AudioMorphology/Europi/kicad/europi_main_v2/europi main v2 board front.png

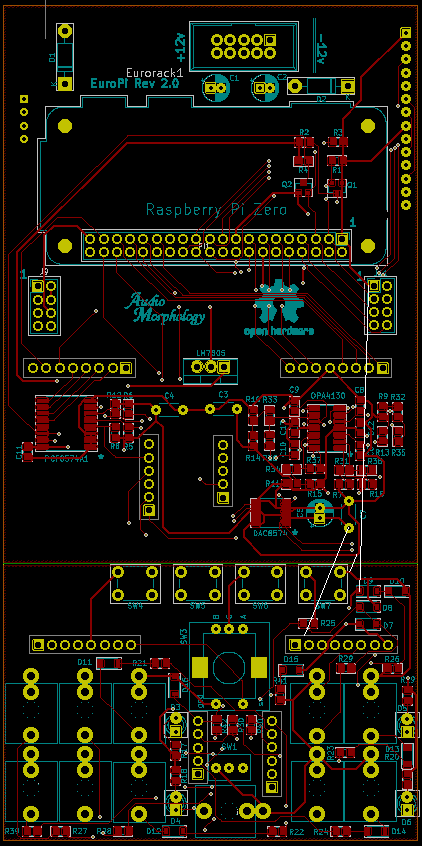
kicad/europi_main_v2/europi main v2 board front.png
