AudioMorphology/Europi/kicad/europi_main_v2/europi main v2 board rear.png

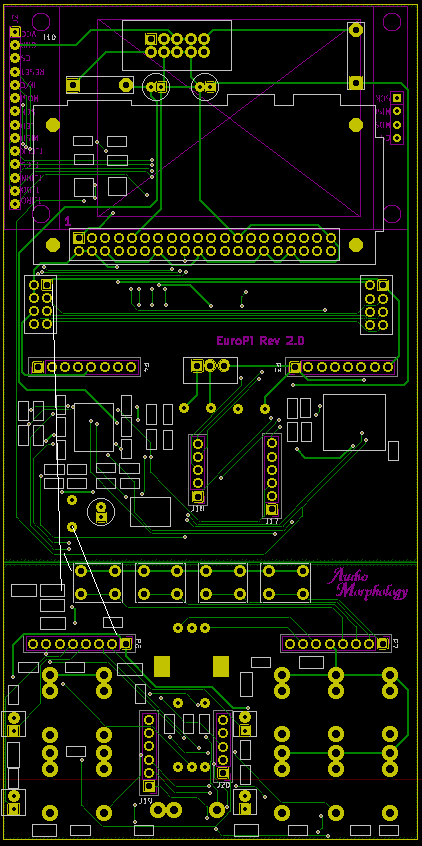
kicad/europi_main_v2/europi main v2 board rear.png
