AudioMorphology/Europi/quantizer_scales.h

// Copyright 2016 Richard R. Goodwin / Audio Morphology / Olivier Gillet
//
// Authors: Richard R. Goodwin (richard.goodwin@morphology.co.uk)
//          Olivier Gillet (ol.gillet@gmail.com)
//
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
// See http://creativecommons.org/licenses/MIT/ for more information.
//-------------------------------------------------------------------------------

// The values in the scale_values array and, indeed, the names of the various scales
// came from the Mutable Instruments Braids software, released by Olivier Gillet 
// under a CC License. So, I have incorporated the same license, and have included 
// Olivier's License declaration, below, to make it clear that I am not claiming 
// ownership or proprietary rights over any aspects of these quantisation scales

//-------------------------------------------------------------------------------
// Copyright 2015 Olivier Gillet.
//
// Author: Olivier Gillet (ol.gillet@gmail.com)
//
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
// See http://creativecommons.org/licenses/MIT/ for more information.
//
// -----------------------------------------------------------------------------

/*
 * QUANTIZATION SCALES
 * 
 * These arrays set the Lower and Upper boundaries for
 * a given note in a given scale, and identify the absolute
 * value that should be returned.
 * 
 * Values are based on 6000 discrete values per Octave
 */

static int lower_boundary[49][12] = {
{0},
{0,250,750,1250,1750,2250,2750,3250,3750,4250,4750,5250},
{0,500,1500,2250,3000,4000,5000},
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
{0,1020,1930,2488,3512,3961,5441},
//43: m_kauns
{0,1020,2039,2488,3961,4980},
//44: Bairagi
{0,449,2488,3512,4980},
//45: b_todi
{0,449,1469,3512,4980},
//46: Chandradeep
{0,1469,2488,3512,4980},
//47: Kaushik_todi
{0,1469,2488,2949,3961},
//48: Jogeshwari
{0,1469,1930,2488,4422,4980}
};


// Number of Notes in each particular scale
static int scale_notes[49] = {
  // Off
  0,
  // Semitones
  12,
  // Ionian (From midipal/BitT source code)
  7,
  // Dorian (From midipal/BitT source code)
  7,
  // Phrygian (From midipal/BitT source code)
  7,
  // Lydian (From midipal/BitT source code)
  7,
  // Mixolydian (From midipal/BitT source code)
  7,
  // Aeolian (From midipal/BitT source code)
  7,
  // Locrian (From midipal/BitT source code)
  7,
  // Blues major (From midipal/BitT source code)
  6,
  // Blues minor (From midipal/BitT source code)
  6,
  // Pentatonic major (From midipal/BitT source code)
  5,
  // Pentatonic minor (From midipal/BitT source code)
  5,
  // Folk (From midipal/BitT source code)
  8,
  // Japanese (From midipal/BitT source code)
  5,
  // Gamelan (From midipal/BitT source code)
  5,
  // Gypsy
  7,
  // Arabian
  7,
  // Flamenco
  7,
  // Whole tone (From midipal/BitT source code)
  6,
  // pythagorean (From yarns source code)
  12,
  // 1_4_eb (From yarns source code)
  12,
  // 1_4_e (From yarns source code)
  12,
  // 1_4_ea (From yarns source code)
  12,
  // bhairav (From yarns source code)
  7,
  // gunakri (From yarns source code)
  5,
  // marwa (From yarns source code)
  6,
  // shree (From yarns source code)
  7,
  // purvi (From yarns source code)
  7,
  // bilawal (From yarns source code)
  7,
  // yaman (From yarns source code)
  7,
  // kafi (From yarns source code)
  7,
  // bhimpalasree (From yarns source code)
  7,
  // darbari (From yarns source code)
  7,
  // rageshree (From yarns source code)
  7,
  // khamaj (From yarns source code)
  8,
  // mimal (From yarns source code)
  8,
  // parameshwari (From yarns source code)
  6,
  // rangeshwari (From yarns source code)
  6,
  // gangeshwari (From yarns source code)
  6,
  // kameshwari (From yarns source code)
  6,
  // pa__kafi (From yarns source code)
  7,
  // natbhairav (From yarns source code)
  7,
  // m_kauns (From yarns source code)
  6,
  // bairagi (From yarns source code)
  5,
  // b_todi (From yarns source code)
  5,
  // chandradeep (From yarns source code)
  5,
  // kaushik_todi (From yarns source code)
  5,
  // jogeshwari (From yarns source code)
  6
};

// Array of strings representing the name of each scale
static const char * scale_names[] = {
"Off",
"Semitones",
"Ionian",
"Dorian",
"Phrygian", 
"Lydian",
"Mixolydian",
"Aeolian", 
"Locrian", 
"Blues Major", 
"Blues Minor", 
"Pentatonic Major", 
"Pentatonic Minor", 
"Folk", 
"Japanese", 
"Gamelan", 
"Gypsy", 
"Arabian", 
"Flamenco", 
"Whole Tone", 
"Pythagorean", 
"1_4_eb", 
"1_4_e", 
"1_4_ea", 
"bhairav", 
"Gunakri", 
"Marwa", 
"Shree", 
"Purvi", 
"Bilawal", 
"Kafi", 
"Bhimpalascree", 
"Darbari", 
"Rageshree", 
"Khamaj", 
"Mimal", 
"Parameshwari", 
"Rangeshwari", 
"Gangeshwari", 
"Kameshwari", 
"pa__kafi", 
"Natbhairav", 
"m_kauns", 
"Bairagi", 
"b_todi", 
"Chandradeep", 
"Kaushik_todi", 
"Jogeshwari"
};
