AudioMorphology/Europi/bjorklund.h

// Copyright 2016 Richard R. Goodwin / Audio Morphology / Tim Churches
//
// Authors: Richard R. Goodwin (richard.goodwin@morphology.co.uk)
//          Tim Churches: https://github.com/timchurches
//
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
// See http://creativecommons.org/licenses/MIT/ for more information.
//-------------------------------------------------------------------------------

// The values in the tables below were computed by Tim Churches using a Python
// implementation of E. Bjorklund's algorithm from his paper entitled 'The Theory 
// of Rep-Rate Pattern Generation in the SNS Timing Systems' and released under 
// the licence below, which I include in full.

//--------------------------------------------------------------------------------
// Copyright (c) 2016 Tim Churches
//
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
// Bjorklund (Euclidean) patterns, generated by resources/bjorklund.py

/* All that these are are bit-wise patterns representing the 'most symmetrical' 
 * distribution of a given number of triggers within a given number of beats.
 * 
 * Bjorklund's aglorithm uses a recursive method for dividing beats into steps
 * and then dividing any remaining beats into those etc etc.
 * 
 * The end result is surprisingly musical, and generates rhythms that are 
 * recognisable from various cultures.
 */
static uint32_t bjorklund_patterns[31][33] = {
// 2 step patterns
{0,1,3,0,0,0,0,0,0,0,0,0,0,0,0,0,0,0,0,0,0,0,0,0,0,0,0,0,0,0,0,0,0 }, 
// 3 step patterns
{0,1,3,7,0,0,0,0,0,0,0,0,0,0,0,0,0,0,0,0,0,0,0,0,0,0,0,0,0,0,0,0,0 }, 
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
{0,1,16385,1049601,2113665,17043521,34636833,17895697,71600273,71901769,153391689,153692457,88757413,156543573,89478485,357913941,223783765,359356085,229485997,230087533,249263835,250469819,393705335,259776247,264174575,401596351,268173055,402644991,268435455,536870911,0,0,0},
// 30 step patterns
{0,1,32769,1049601,4227201,17043521,34636833,69345553,143167761,76620873,153391689,306858313,173184165,312822421,178951509,357913941,715838805,448096981,727373493,460025197,460175067,767258331,501070779,518977399,519552495,528349151,803200959,536346111,536854527,536870911,1073741823,0,0},
// 31 step patterns
{0,1,32769,1049601,16843009,17043521,34636833,138682897,286331153,287458441,153391689,345133641,614802729,623530661,357739093,357913941,1431655765,1432005461,900422325,917878189,1457216365,1533916891,997649883,1002159035,1038020471,1593294319,1602090975,1069531071,1610087935,1610596351,1073741823,2147483647,0},
// 32 step patterns
{0,1,65537,4196353,16843009,67641409,69272609,142885409,286331153,304367761,306778697,1227133513,1229539657,1246925989,1251297941,1252693333,1431655765,1789580629,1792371413,1801115317,1835887981,1840700269,3067852507,3077496251,2004318071,3151884023,3186605551,2130442207,2139062143,2146434559,2147450879,2147483647,4294967295 }
};
