AudioMorphology/Europi/europi_gui.c

// Copyright 2016 Richard R. Goodwin / Audio Morphology
//
// Author: Richard R. Goodwin (richard.goodwin@morphology.co.uk)
//
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
// See http://creativecommons.org/licenses/MIT/ for more information.

#include <stdio.h>
#include <string.h>
#include "europi.h"
#include "../raylib/src/raylib.h"

extern int clock_freq;
extern int step_ticks;
extern int prog_running;
extern int run_stop; 
extern int save_run_stop;
extern int last_track;
extern int SingleChannelOffset;
extern Vector2 touchPosition;
extern int currentGesture;
extern int lastGesture;
extern menu Menu[]; 
extern char input_txt[]; 
extern char current_filename[];
extern char modal_dialog_txt1[];
extern char modal_dialog_txt2[];
extern char modal_dialog_txt3[];
extern char modal_dialog_txt4[];
extern Texture2D KeyboardTexture;
extern Texture2D DialogTexture;
extern Texture2D SmallDialogTexture;
extern Texture2D TextInputTexture;
extern Texture2D Text2chTexture;
extern Texture2D Text5chTexture;
extern Texture2D Text10chTexture;
extern Texture2D MainScreenTexture;
extern Texture2D TopBarTexture;
extern Texture2D ButtonBarTexture; 
extern Texture2D VerticalScrollBarTexture;
extern Texture2D VerticalScrollBarShortTexture;
extern Texture2D ScrollHandleTexture;
extern int VerticalScrollPercent;
extern char *kbd_chars[4][11];
extern char debug_messages[10][80];
extern int next_debug_slot;
extern int kbd_char_selected;
extern int selected_step;
extern enum encoder_focus_t encoder_focus;
extern enum btnA_func_t btnA_func;
extern enum btnB_func_t btnB_func;
extern enum btnC_func_t btnC_func;
extern enum btnD_func_t btnD_func;
extern int btnA_state;
extern int btnB_state;
extern int btnC_state;
extern int btnD_state;
extern int edit_track;
extern int edit_step;
//extern struct screen_overlays ScreenOverlays;
extern uint32_t ActiveOverlays;
extern enum display_page_t DisplayPage;
extern struct europi Europi;
extern char **files;
extern size_t file_count;                      
extern int file_selected;
extern int first_file;
extern int debug;
extern pthread_attr_t detached_attr;		
extern pthread_t ThreadId; 


/*
 * GUI_8x8 Attempts to display more detail in a subset of tracks and steps
 * 8 Tracks x 8 Steps
 */
void gui_8x8(void){
    Rectangle stepRectangle = {0,0,0,0};
    Rectangle trackRectangle = {0,0,0,0};
    int start_track,track, column;
    int step, offset, txt_len;
    char txt[20]; 
    /* Depending on the total number of tracks, and the position 
     * of the vertical scroll bar, the starting track will vary
     */
    if(last_track > 8){
        start_track = ((last_track-8) * VerticalScrollPercent) / 100;
        /* Don't display the Vertical Scroll Bar in certain situations */
        if(ActiveOverlays & ovl_Keyboard) { 
			ActiveOverlays &= ~ovl_VerticalScrollBar;
        }
        else {
            ActiveOverlays |= ovl_VerticalScrollBar;
        }
    }
    else {
        start_track = 0;
        ActiveOverlays &= ~ovl_VerticalScrollBar;
    }
    BeginDrawing();
    DrawTexture(MainScreenTexture,0,0,WHITE);
	int vOffset = 0;
	if(ShortScroll()) vOffset=20;
    for(track = 0; track < 8; track++){
        // Can only display 8 tracks, so need to know which
        // track we are starting with, and display the next 7
        offset = Europi.tracks[start_track+track].current_step / 8;
        sprintf(txt,"%02d-%d:",start_track+track+1,(offset * 8)+1);
        txt_len = MeasureText(txt,20);
        if(start_track+track < last_track){
            DrawText(txt,68-txt_len,12+(vOffset+(track * 25)),20,DARKGRAY);
            DrawRectangleLines(4,vOffset+8+(track * 25),67,26,DARKGRAY);
        } else {
            // in-active tracks greyed-out
            DrawText(txt,68-txt_len,12+(vOffset+(track * 25)),20,LIGHTGRAY);
            DrawRectangleLines(4,vOffset+8+(track * 25),67,26,LIGHTGRAY);
        }
        // Check for Track select
        trackRectangle.x = 4;
        trackRectangle.y = vOffset + 8 + (track * 25);
        trackRectangle.width = 67;
        trackRectangle.height = 26;
		// Only if no menus or overlays active, and this track isn't beyond the end track
		if (CheckCollisionPointRec(touchPosition, trackRectangle) && (currentGesture != GESTURE_NONE) && (start_track+track < last_track)){
			if(OverlayActive( ovl_VerticalScrollBar ) == 0){
                // Open this track in a Single Channel view
                edit_track = start_track+track;
                select_track(start_track+track);
                ClearScreenOverlays();
                SwitchChannelFunction(edit_track);
				encoder_focus = track_select;
            }
			else {
				// Just update the selected track
				select_track(start_track+track);
				encoder_focus = track_select;
			}
        }
        for(column=0;column<8;column++){
            stepRectangle.x = 70 + (column * 25);
            stepRectangle.y = vOffset + 10 + (track * 25);
            stepRectangle.width = 22;
            stepRectangle.height = 22;
            if(start_track+track < last_track) {
                // Check gesture collision
                if (CheckCollisionPointRec(touchPosition, stepRectangle) && (currentGesture == GESTURE_DOUBLETAP)){
                    if(OverlayActive(ovl_VerticalScrollBar) == 0){
                    // Only if no Menus or Overlays active
                        // Open this step in the Single Step editor
                        edit_track = start_track+track;
                        edit_step = (offset*8)+column;
                        select_track(start_track+track);
                        ClearScreenOverlays();
                        DisplayPage = SingleStep;
                        ActiveOverlays |= ovl_SingleStep; 
                        encoder_focus = step_select;
                        btnA_func = btnA_none;
                        btnB_func = btnB_prev;
                        btnC_func = btnC_next;
                        btnD_func = btnD_done; 
                        save_run_stop = run_stop;
                    }
                    else {
                        select_track(start_track+track);
                        edit_step = (offset*8)+column;
                        encoder_focus = step_select;
                    }
                }
                if((offset*8)+column >= Europi.tracks[start_track+track].last_step){
                    // beyond the last step, just paint black squares
                    DrawRectangleRec(stepRectangle, BLACK); 
                }
                else if((offset*8)+column == Europi.tracks[start_track+track].current_step){
                    // Paint current step
                    DrawRectangleRec(stepRectangle, LIME);   
                }
                else {
                    // paint blank step
                    DrawRectangleRec(stepRectangle, MAROON); 
                }
            }
            else {
                DrawRectangleRec(stepRectangle,LIGHTGRAY);
            }
        }  
        // Print the end-step number at the RHS of each row
        sprintf(txt,":%d",(offset * 8)+8);
        if(start_track+track < last_track) {
            DrawText(txt,270,12+(vOffset+(track * 25)),20,DARKGRAY);
        }
        else {
            DrawText(txt,270,12+(vOffset+(track * 25)),20,LIGHTGRAY);
        }
    }
    // Handle any screen overlays - these need to 
    // be added within the Drawing loop
    ShowScreenOverlays();
    EndDrawing();
}
/*
 * GUI_SINGLESTEP enables editing of all params 
 * to do with a single step
 */
void gui_singlestep(void){
    int column, offset, txt_len;
    char txt[20]; 
    Rectangle stepRectangle = {0,0,0,0};
    Rectangle touchRectangle = {0,0,0,0};
    BeginDrawing();
    DrawTexture(MainScreenTexture,0,0,WHITE);
    // Items to cover:
    // Track Type (CV / MIDI)
    // Quantization
    // Pitch
    // Gate / Trigger
    // Slew
    // Step Repeat
    // DrawRectangle(6,29, 308, 183, CLR_LIGHTBLUE);  
    // Draw the current Track 8-Step segement
    offset = edit_step / 8; //Europi.tracks[edit_track].current_step / 8;
    sprintf(txt,"%02d-%d:",edit_track+1,(offset * 8)+1);
    txt_len = MeasureText(txt,20);
    DrawText(txt,68-txt_len,34,20,DARKGRAY);
	// Check for tap on this to switch to Track view
	touchRectangle.x = 8;
	touchRectangle.y = 34;
	touchRectangle.width = 60;
	touchRectangle.height = 20;
	if (CheckCollisionPointRec(touchPosition, touchRectangle) && (currentGesture != GESTURE_NONE)){
		// Switch to Track View
		ClearScreenOverlays();
		SwitchChannelFunction(edit_track);
		encoder_focus = track_select;		
	}
    for(column=0;column<8;column++){
        stepRectangle.x = 70 + (column * 25);
        stepRectangle.y = 33;
        stepRectangle.width = 22;
        stepRectangle.height = 22;
        // Check gesture collision
        if (CheckCollisionPointRec(touchPosition, stepRectangle) && (currentGesture != GESTURE_NONE)){
            // Open this step in the Single Step editor
            edit_step = (offset*8)+column;
            ClearScreenOverlays();
            DisplayPage = SingleStep;
            ActiveOverlays |= ovl_SingleStep;
            encoder_focus = step_select;
            btnA_func = btnA_none;
            btnB_func = btnB_prev;
            btnC_func = btnC_next;
            btnD_func = btnD_done; 
            save_run_stop = run_stop;
        }
        else {
            if((offset*8)+column == Europi.tracks[edit_track].last_step){
                // Paint last step
                DrawRectangleRec(stepRectangle, BLACK); 
            }
            else if((offset*8)+column == Europi.tracks[edit_track].current_step){
                // Paint current step
                DrawRectangleRec(stepRectangle, LIME);   
            }
            else if((offset*8)+column == edit_step){
                // Paint step currently being edited
                DrawRectangleRec(stepRectangle, YELLOW);   
            }
            else {
                // paint blank step
                DrawRectangleRec(stepRectangle, MAROON); 
            }
        } 
    }  
    // Print the end-step number at the RHS of each row
    sprintf(txt,":%d",(offset * 8)+8);
    DrawText(txt,270,34,20,DARKGRAY);
    touchRectangle.x = 8;
    touchRectangle.height = 20;
	// Slew Type
    touchRectangle.y = 58;
    switch(Europi.tracks[edit_track].channels[CV_OUT].steps[edit_step].slew_type){
        default:
        case Off:
            DrawText("Off",140,58,20,BLUE);
			touchRectangle.width = 2;
			DrawRectangleRec(touchRectangle, LIGHTGRAY);
        break;
        case Linear:
			touchRectangle.width = 16;
			DrawRectangleRec(touchRectangle, LIGHTGRAY);
            DrawText("Linear",140,58,20,BLUE);
        break;
        case Exponential:
			touchRectangle.width = 32;
			DrawRectangleRec(touchRectangle, LIGHTGRAY);
            DrawText("Exponential",140,58,20,BLUE);
        break;
        case RevExp:
			touchRectangle.width = 48;
			DrawRectangleRec(touchRectangle, LIGHTGRAY);
            DrawText("Reverse Exp",140,58,20,BLUE);
        break;
        case Log:
			touchRectangle.width = 64;
			DrawRectangleRec(touchRectangle, LIGHTGRAY);
            DrawText("Logarithmic",140,58,20,BLUE);
        break;
		case RevLog:
			touchRectangle.width = 80;
			DrawRectangleRec(touchRectangle, LIGHTGRAY);
            DrawText("Reverse Log",140,58,20,BLUE);
        break;
        case Sine:
			touchRectangle.width = 96;
			DrawRectangleRec(touchRectangle, LIGHTGRAY);
            DrawText("Sine",140,58,20,BLUE);
        break;
        case RevSine:
			touchRectangle.width = 112;
			DrawRectangleRec(touchRectangle, LIGHTGRAY);
            DrawText("Reverse Sine",140,58,20,BLUE);
        break;
        case Cosine:
			touchRectangle.width = 128;
			DrawRectangleRec(touchRectangle, LIGHTGRAY);
            DrawText("Cosine",140,58,20,BLUE);
        break;
    }
	touchRectangle.width = 128;
	DrawText("Slew Type:",30,58,20,DARKGRAY);
	if (CheckCollisionPointRec(touchPosition, touchRectangle) && (currentGesture != GESTURE_NONE)){
		// Work out what % of the way along the touchRectangle we are
		 switch((int)(((touchPosition.x - 8) / (float)128) * 8)){
				default:
				case 0:
						Europi.tracks[edit_track].channels[CV_OUT].steps[edit_step].slew_type = Off;
				break;
				case 1:
						Europi.tracks[edit_track].channels[CV_OUT].steps[edit_step].slew_type = Linear;
				break;
				case 2:
						Europi.tracks[edit_track].channels[CV_OUT].steps[edit_step].slew_type = Exponential;
				break;
				case 3:
						Europi.tracks[edit_track].channels[CV_OUT].steps[edit_step].slew_type = RevExp;
				break;
				case 4:
						Europi.tracks[edit_track].channels[CV_OUT].steps[edit_step].slew_type = Log;
				break;
				case 5:
						Europi.tracks[edit_track].channels[CV_OUT].steps[edit_step].slew_type = RevLog;
				break;
				case 6:
						Europi.tracks[edit_track].channels[CV_OUT].steps[edit_step].slew_type = Sine;
				break;
				case 7:
						Europi.tracks[edit_track].channels[CV_OUT].steps[edit_step].slew_type = RevSine;
				break;
				case 8:
						Europi.tracks[edit_track].channels[CV_OUT].steps[edit_step].slew_type = Cosine;
				break;
		 }
	}

	// Slew Shape
	touchRectangle.y = 78;
    if(Europi.tracks[edit_track].channels[CV_OUT].steps[edit_step].slew_type != Off){
        //Only draw the shape if the Slew Type isn't Off
        switch(Europi.tracks[edit_track].channels[CV_OUT].steps[edit_step].slew_shape){
            default:
            case Both:
				touchRectangle.width = 4;
				DrawRectangleRec(touchRectangle, LIGHTGRAY);
                DrawText("Both",140,78,20,BLUE);
            break;
            case Rising:
				touchRectangle.width = 64;
				DrawRectangleRec(touchRectangle, LIGHTGRAY);
                DrawText("Rising",140,78,20,BLUE);
            break;
            case Falling:
				touchRectangle.width = 128;
				DrawRectangleRec(touchRectangle, LIGHTGRAY);
                DrawText("Falling",140,78,20,BLUE);
             break;
        }
    }
	touchRectangle.width = 128;
    DrawText("Slew Shape:",20,78,20,DARKGRAY);

	if (CheckCollisionPointRec(touchPosition, touchRectangle) && (currentGesture != GESTURE_NONE)){
		// Work out what % of the way along the touchRectangle we are
		 switch((int)(((touchPosition.x - 8) / (float)128) * 3)){
				default:
				case 0:
						Europi.tracks[edit_track].channels[CV_OUT].steps[edit_step].slew_shape = Both;
				break;
				case 1:
						Europi.tracks[edit_track].channels[CV_OUT].steps[edit_step].slew_shape = Rising;
				break;
				case 2:
						Europi.tracks[edit_track].channels[CV_OUT].steps[edit_step].slew_shape = Falling;
				break;
		 }
	}

	// Slew Length
    if(Europi.tracks[edit_track].channels[CV_OUT].steps[edit_step].slew_type != Off){
        sprintf(txt,"%d",Europi.tracks[edit_track].channels[CV_OUT].steps[edit_step].slew_length);
        DrawText(txt,140,98,20,BLUE); 
    }
	touchRectangle.y = 98;
	touchRectangle.width = (int)((Europi.tracks[edit_track].channels[CV_OUT].steps[edit_step].slew_length/(float)500000)*128);
	DrawRectangleRec(touchRectangle, LIGHTGRAY);
    DrawText("Slew Length:",12,98,20,DARKGRAY);
	touchRectangle.width = 128;
	if (CheckCollisionPointRec(touchPosition, touchRectangle) && (currentGesture != GESTURE_NONE)){
		// Work out what % of the way along the touchRectangle we are
		Europi.tracks[edit_track].channels[CV_OUT].steps[edit_step].slew_length = (int)(((float)(touchPosition.x - 8) / (float)128) * (float)500000);
	}
	
   
	touchRectangle.y = 118;
    switch(Europi.tracks[edit_track].channels[GATE_OUT].steps[edit_step].gate_type){
        default:
        case Gate_Off:
			touchRectangle.width = 4;
			DrawRectangleRec(touchRectangle, LIGHTGRAY);
            DrawText("Off",140,118,20,BLUE);
        break;
        case Gate_On:
			touchRectangle.width = 24;
			DrawRectangleRec(touchRectangle, LIGHTGRAY);
            DrawText("On",140,118,20,BLUE);
        break;
        case Trigger:
			touchRectangle.width = 44;
			DrawRectangleRec(touchRectangle, LIGHTGRAY);
            DrawText("Trigger",140,118,20,BLUE);
        break;
        case Gate_25:
			touchRectangle.width = 64;
			DrawRectangleRec(touchRectangle, LIGHTGRAY);
            DrawText("25%",140,118,20,BLUE);
        break;
        case Gate_50:
			touchRectangle.width = 84;
			DrawRectangleRec(touchRectangle, LIGHTGRAY);
            DrawText("50%",140,118,20,BLUE);
        break;
        case Gate_75:
			touchRectangle.width = 104;
			DrawRectangleRec(touchRectangle, LIGHTGRAY);
            DrawText("75%",140,118,20,BLUE);
        break;
        case Gate_95:
			touchRectangle.width = 128;
			DrawRectangleRec(touchRectangle, LIGHTGRAY);
            DrawText("95%",140,118,20,BLUE);
        break;
    }
    DrawText("Gate Type:",26,118,20,DARKGRAY);
	touchRectangle.width = 128;
		if (CheckCollisionPointRec(touchPosition, touchRectangle) && (currentGesture != GESTURE_NONE)){
		// Work out what % of the way along the touchRectangle we are
		 switch((int)(((touchPosition.x - 8) / (float)128) * 6)){
				default:
				case 0:
						Europi.tracks[edit_track].channels[GATE_OUT].steps[edit_step].gate_type = Gate_Off;
				break;
				case 1:
						Europi.tracks[edit_track].channels[GATE_OUT].steps[edit_step].gate_type = Gate_On;
				break;
				case 2:
						Europi.tracks[edit_track].channels[GATE_OUT].steps[edit_step].gate_type = Trigger;
				break;
				case 3:
						Europi.tracks[edit_track].channels[GATE_OUT].steps[edit_step].gate_type = Gate_25;
				break;
				case 4:
						Europi.tracks[edit_track].channels[GATE_OUT].steps[edit_step].gate_type = Gate_50;
				break;
				case 5:
						Europi.tracks[edit_track].channels[GATE_OUT].steps[edit_step].gate_type = Gate_75;
				break;
				case 6:
						Europi.tracks[edit_track].channels[GATE_OUT].steps[edit_step].gate_type = Gate_95;
				break;
		 }
	}



    sprintf(txt,"%d",Europi.tracks[edit_track].channels[GATE_OUT].steps[edit_step].ratchets);
    DrawText(txt,140,138,20,BLUE);   
    touchRectangle.y = 138;
	touchRectangle.width = (int)((Europi.tracks[edit_track].channels[GATE_OUT].steps[edit_step].ratchets/(float)16)*128);
	DrawRectangleRec(touchRectangle, LIGHTGRAY);
    DrawText("Ratchets:",40,138,20,DARKGRAY);
	touchRectangle.width = 128;
    if (CheckCollisionPointRec(touchPosition, touchRectangle) && (currentGesture != GESTURE_NONE)){
		// Work out what % of the way along the touchRectangle we are
		Europi.tracks[edit_track].channels[GATE_OUT].steps[edit_step].ratchets = (int)(((touchPosition.x - 8) / (float)128) * 16);
	}
	
    sprintf(txt,"%d",Europi.tracks[edit_track].channels[GATE_OUT].steps[edit_step].fill);
    DrawText(txt,140,158,20,BLUE);    
    touchRectangle.y = 158;
	touchRectangle.width = (int)((Europi.tracks[edit_track].channels[GATE_OUT].steps[edit_step].fill/(float)16)*128);
	DrawRectangleRec(touchRectangle, LIGHTGRAY);
    DrawText("Fill:",104,158,20,DARKGRAY);
	touchRectangle.width = 128;
    if (CheckCollisionPointRec(touchPosition, touchRectangle) && (currentGesture != GESTURE_NONE)){
		// Work out what % of the way along the touchRectangle we are
		Europi.tracks[edit_track].channels[GATE_OUT].steps[edit_step].fill = (int)(((touchPosition.x - 8) / (float)128) * 16);
	}

    // Draw the Pitch 'Bar Graph' display
    DrawRectangleLines(280,81,20,120,BLACK);
    int Octave,Partial,Pitch,i;
    Octave = Europi.tracks[edit_track].channels[CV_OUT].steps[edit_step].raw_value / 6000;
    Partial = Europi.tracks[edit_track].channels[CV_OUT].steps[edit_step].raw_value % 6000;
    //Check for collision within the Partial bar. Note: Ignores touches in left-most 5 pixels
    stepRectangle.x = 280+5;
    stepRectangle.y = 81;
    stepRectangle.width = 20-5;
    stepRectangle.height = 120;
    if (CheckCollisionPointRec(touchPosition, stepRectangle) && (currentGesture != GESTURE_NONE)){
        // Work out how far up the Partial bar we are
        if((touchPosition.y >= (float)81) && (touchPosition.y <= (float)(81+120))) {
            Partial = (int)(((120-(touchPosition.y - (float)81)) / (float)(120)) * 5999);
            int newpitch = quantize((6000 * Octave) + Partial,Europi.tracks[edit_track].channels[CV_OUT].quantise);
            Europi.tracks[edit_track].channels[CV_OUT].steps[edit_step].raw_value = newpitch;
            // Update scaled value 
            Europi.tracks[edit_track].channels[CV_OUT].steps[edit_step].scaled_value = scale_value(edit_track,newpitch);
        }
    }

    for(i=0;i<10;i++){
        DrawRectangleLines(260,(i*12)+83,15,10,BLACK);
        if((9-i) == Octave){
            // Colour the current Octave
            DrawRectangle(261,(i*12)+83+1,13,8,RED);
        }
        //Check for collision within the Octave Bar
        stepRectangle.x = 260;
        stepRectangle.y = (i*12)+83;
        stepRectangle.width = 15;
        stepRectangle.height = 10;
        if (CheckCollisionPointRec(touchPosition, stepRectangle) && (currentGesture != GESTURE_NONE)){
            // Set the Octave for this Step & Quantize the RAW value
            int newpitch = quantize((6000 * (9-i)) + Partial,Europi.tracks[edit_track].channels[CV_OUT].quantise);
            Europi.tracks[edit_track].channels[CV_OUT].steps[edit_step].raw_value = newpitch;
            // Update scaled value 
            Europi.tracks[edit_track].channels[CV_OUT].steps[edit_step].scaled_value = scale_value(edit_track,newpitch);
        }
    }
    // Fill the partial column = this is the percentage of an 
    // Octave, so 6000 would == 120 pixels
    Pitch = (Partial * 120) / 6000;
    DrawRectangle(281,81+120-Pitch-1,18,Pitch,BLUE); 
  

    // Draw all Steps in the track along the bottom of the screen
    int x = 14;
    int step;
    for(step = 0; step<Europi.tracks[edit_track].last_step; step++){
        if(step == offset * 8){
            //Highlight behind current block of 8 steps
            touchRectangle.x = x+1;
            touchRectangle.y = 202;
            touchRectangle.width = 8*9+1;
            touchRectangle.height = 10;
            DrawRectangleRec(touchRectangle,DARKGRAY);
            x += 2;
        }
        if (step == ((offset*8)+8)) x+= 2;
        touchRectangle.x = x;
        touchRectangle.y = 203;
        touchRectangle.width = 8;
        touchRectangle.width = 8;
        touchRectangle.height = 8;
        if(step == edit_step){
            DrawRectangleRec(touchRectangle,YELLOW);
        }
        else if(step == Europi.tracks[edit_track].current_step){
            DrawRectangleRec(touchRectangle,LIME);
        }
        else{
            DrawRectangleRec(touchRectangle,RED);
        }
        if (CheckCollisionPointRec(touchPosition, touchRectangle) && (currentGesture != GESTURE_NONE)){
            //Move the displayed 8-step segment to this position
            edit_step = step;
        }
        x += 9;
    }
    // Handle any screen overlays - these need to 
    // be added within the Drawing loop
    ShowScreenOverlays();
    EndDrawing();
}


/*
 * gui_SingleChannel displays just the currently
 * selected channel on a page of its own, but only
 * in blocks of 8 steps
 */
void gui_SingleChannel(void){
    Rectangle touchRectangle = {0,0,0,0};
    int track, step, column, i;
    int Octave, Partial, Pitch;
    char track_no[20];
    char step_no[5];
    int txt_len;
    int row;
    Rectangle stepRectangle = {0,0,0,0};
    BeginDrawing();
    DrawTexture(MainScreenTexture,0,0,WHITE);
    for(track = 0; track < last_track; track++){
        if(Europi.tracks[track].selected == TRUE){
            for(column = 0; column < 8; column++){
                Octave = Europi.tracks[track].channels[CV_OUT].steps[SingleChannelOffset+column].raw_value / 6000;
                Partial = Europi.tracks[track].channels[CV_OUT].steps[SingleChannelOffset+column].raw_value % 6000;
                //Check for collision within the Partial bar
                //Note: This ignores touches close to the left-hand
                //edge, to reduce the accidental selection of octaves
                touchRectangle.x = 22+(column*39)+5;
                touchRectangle.y = 30;
                touchRectangle.width = 18-5;    
                touchRectangle.height = 120;
                if (CheckCollisionPointRec(touchPosition, touchRectangle) && (currentGesture != GESTURE_NONE)){
                    // Work out how far up the Partial bar we are
                    if((touchPosition.y >= (float)30) && (touchPosition.y <= (float)(30+120))) {
                        Partial = (int)(((120-(touchPosition.y - (float)30)) / (float)(120)) * 5999);
                        int newpitch = quantize((6000 * Octave) + Partial,Europi.tracks[track].channels[CV_OUT].quantise);
                        Europi.tracks[track].channels[CV_OUT].steps[SingleChannelOffset+column].raw_value = newpitch;
                        // Update scaled value 
                        Europi.tracks[track].channels[CV_OUT].steps[SingleChannelOffset+column].scaled_value = scale_value(track,newpitch);
                    }
                }
                //Column of Octave buttons
                for(i=0;i<10;i++){
                    DrawRectangleLines(6+(column*39),(i*12)+32,15,10,BLACK);
                    if((9-i) == Octave){
                        // Colour the current Octave
                        if(SingleChannelOffset+column == Europi.tracks[track].current_step){
                            DrawRectangle(6+(column*39)+1,(i*12)+32+1,13,8,LIME);
                        }
                        else{
                            DrawRectangle(6+(column*39)+1,(i*12)+32+1,13,8,RED);
                        }
                    }
                    //Check for collision within the Octave Bar
                    touchRectangle.x = 6+(column*39);
                    touchRectangle.y = (i*12)+32;
                    touchRectangle.width = 15;
                    touchRectangle.height = 10;
					// Octave buttons only respond to tap, not any old gesture
                    if (CheckCollisionPointRec(touchPosition, touchRectangle) && (currentGesture == GESTURE_TAP)){
                        // Set the Octave for this Step & Quantize the RAW value
                        int newpitch = quantize((6000 * (9-i)) + Partial,Europi.tracks[track].channels[CV_OUT].quantise);
                        Europi.tracks[track].channels[CV_OUT].steps[SingleChannelOffset+column].raw_value = newpitch;
                        // Update scaled value 
                        Europi.tracks[track].channels[CV_OUT].steps[SingleChannelOffset+column].scaled_value = scale_value(track,newpitch);
                    }

                }
                // Fill the partial column = this is the percentage of an 
                // Octave, so 6000 would == 120 pixels
                Pitch = (Partial * 120) / 6000;
                if(SingleChannelOffset+column == Europi.tracks[track].current_step){
                    DrawRectangle(22+(column*39)+1,30+120-Pitch,16,Pitch,LIME); 
                }
                else {
                    DrawRectangle(22+(column*39)+1,30+120-Pitch,16,Pitch,BLUE); 
                }
                //Fill the column THEN draw the Partial bar, though I actually
                //prefer the display without this box round the partial bar, hence
                //why it is commented out.
                /*DrawRectangleLines(22+(column*39),30,18,120,BLACK);*/
                //Step number boxes
                DrawRectangleLines(6+(column*39),152,33,20,BLACK);
                // Centre the Step Number in the box
                sprintf(step_no,"%d",SingleChannelOffset+column+1);
                txt_len = MeasureText(step_no,20);
                DrawText(step_no,22+(column*39)-(txt_len/2),153,20,DARKGRAY);
                //Check for tap within the Step Number box
                touchRectangle.x = 6+(column*39);
                touchRectangle.y = 160; //Ignores touches in the top few pixels, as it's close to the Partial bar
                touchRectangle.width = 33;
                touchRectangle.height = 12;
                if (CheckCollisionPointRec(touchPosition, touchRectangle) && (currentGesture == GESTURE_TAP)){
                    //Open this Step in the Single Step editor
                    edit_track = track;
                    edit_step = SingleChannelOffset+column;
                    ClearScreenOverlays();
                    DisplayPage = SingleStep;
                    ActiveOverlays |= ovl_SingleStep; 
                    encoder_focus = none;
                    btnA_func = btnA_none;
                    btnB_func = btnB_prev;
                    btnC_func = btnC_next;
                    btnD_func = btnD_done; 
                    save_run_stop = run_stop;

                }
                //Draw the gate lane for this Step
                touchRectangle.y = 175;
                touchRectangle.width = 8;
                touchRectangle.height = 8;
                touchRectangle.x = 6+(column*39);
                Color gate_colour;
                if(SingleChannelOffset+column == Europi.tracks[track].current_step){
                    gate_colour = LIME;
                }
                else{
                    gate_colour = BLUE;
                }
                if(Europi.tracks[track].channels[GATE_OUT].steps[SingleChannelOffset+column].ratchets <= 1){
                    switch(Europi.tracks[track].channels[GATE_OUT].steps[SingleChannelOffset+column].gate_type){
                        case    Gate_On: 
                            touchRectangle.width = 39;
                            DrawRectangleRec(touchRectangle,gate_colour);
                        break;
                        case    Trigger: 
                            touchRectangle.width = 3;
                            DrawRectangleRec(touchRectangle,gate_colour);
                        break;
                        case    Gate_25:
                            touchRectangle.width = 9;
                            DrawRectangleRec(touchRectangle,gate_colour);
                        break;
                        case    Gate_50:
                            touchRectangle.width = 19;
                            DrawRectangleRec(touchRectangle,gate_colour);
                        break;
                        case    Gate_75:
                            touchRectangle.width = 29;
                            DrawRectangleRec(touchRectangle,gate_colour);
                        break;
                        case    Gate_95:
                            touchRectangle.width = 37;
                            DrawRectangleRec(touchRectangle,gate_colour);
                        break;
                        case    Gate_Off:
                        default:
                        break;
                    }
                }
                else {
                    // Ratchetting Gate
                    if(Europi.tracks[track].channels[GATE_OUT].steps[SingleChannelOffset+column].ratchets <= 16){
                        int GateWidth = 38 / Europi.tracks[track].channels[GATE_OUT].steps[SingleChannelOffset+column].ratchets - 1;
                        touchRectangle.width = GateWidth;
                        for(i=0;i<Europi.tracks[track].channels[GATE_OUT].steps[SingleChannelOffset+column].ratchets;i++){
                            if(polyrhythm(Europi.tracks[track].channels[GATE_OUT].steps[SingleChannelOffset+column].ratchets,Europi.tracks[track].channels[GATE_OUT].steps[SingleChannelOffset+column].fill,i)){
                                DrawRectangleRec(touchRectangle,gate_colour);
                            }
                            touchRectangle.x += GateWidth + 1;
                        }
                    }
                    else {
                        // Too many ratchets to show meaningfully, so just draw a 95% fill line
                        touchRectangle.width = 38;
                        DrawRectangleRec(touchRectangle,gate_colour);
                    }
                }
            }
            // Draw all Steps in the track along the bottom of the screen
            int x = 14;
            for(step = 0; step<Europi.tracks[track].last_step; step++){
                if(step == SingleChannelOffset){
                    //Highlight behind current block of 8 steps
                    touchRectangle.x = x+1;
                    touchRectangle.y = 202;
                    touchRectangle.width = 8*9+1;
                    touchRectangle.height = 10;
                    DrawRectangleRec(touchRectangle,DARKGRAY);
                    x += 2;
                }
                if (step == SingleChannelOffset+8) x+= 2;
                touchRectangle.x = x;
                touchRectangle.y = 203;
                touchRectangle.width = 8;
                touchRectangle.height = 8;
                if(step == Europi.tracks[track].current_step){
                    DrawRectangleRec(touchRectangle,LIME);
                }
                else{
                    DrawRectangleRec(touchRectangle,RED);
                }
                if (CheckCollisionPointRec(touchPosition, touchRectangle) && (currentGesture != GESTURE_NONE)){
                    //Move the displayed 8-step segment to this position
                    if(Europi.tracks[track].last_step >= 8){
                        if(step <= (Europi.tracks[track].last_step - 8)) SingleChannelOffset = step;
                        else SingleChannelOffset = Europi.tracks[track].last_step - 8;
                    }
                }
                x += 9;
            }
        }
        
    }
    // Handle any screen overlays - these need to 
    // be added within the Drawing loop
    ShowScreenOverlays();
    EndDrawing();
}
/* gui_SingleAD displays & edits the AD profile for 
 * a track of type SingleAD
 */
void gui_SingleAD(void){
    int track,i,j;
    Vector2 LineStart;
    Vector2 LineEnd;
    Vector2 Origin;
    Vector2 VertexCentre;
    Vector2 ADEnd;
    Rectangle Vertex;
    float x,y;
    
    BeginDrawing();
    DrawTexture(MainScreenTexture,0,0,WHITE);
    for (track = 0; track < MAX_TRACKS; track++){
        if (Europi.tracks[track].selected == TRUE){
            LineStart.x = 8;
            LineStart.y = 20;
            LineEnd.x = 8;
            LineEnd.y = 210;
            // Use the pre-calculated Logarithmic Slew Profile to draw
            // a horizontal log scale
            for(i=0;i<=100;i+=5){
                x = (slew_profiles[0][3][i]*(float)308)/100;
                LineStart.x = 8+(int)x;
                LineEnd.x = 8+(int)x;
                DrawLineEx(LineStart,LineEnd,1,CLR_DARKBLUE);
            }
            // Draw the Curve
            Origin.x = 8;
            Origin.y = 210;

            // Draw the Vertex
            y = Origin.y - 180*((float)Europi.tracks[track].channels[CV_OUT].steps[Europi.tracks[track].current_step].raw_value / (float)60000);
            VertexCentre.x = 100;
            VertexCentre.y = y;
            DrawRectangleLines(VertexCentre.x-4,VertexCentre.y-4,8,8,BLACK);
            
            
            // Draw Rising curve
            LineStart.x = Origin.x;
            LineStart.y = Origin.y - ((slew_profiles[0][7][0]*(float)(Origin.y-VertexCentre.y))/100);
            for(i=1;i<100;i++){
                LineEnd.x = Origin.x+(((VertexCentre.x-Origin.x)*i)/100);
                LineEnd.y = Origin.y - ((slew_profiles[0][7][i]*(float)(Origin.y-VertexCentre.y))/100);
                DrawLineEx(LineStart,LineEnd,1,BLACK);
                LineStart.x = LineEnd.x;
                LineStart.y = LineEnd.y;
            }
            //Make sure graph actually arrives in the Vertex
            DrawLineEx(LineStart,VertexCentre,1,BLACK);
            
            // Draw Falling curve
            ADEnd.x = 200;
            ADEnd.y = 210;
            LineStart.x = VertexCentre.x;
            LineStart.y = VertexCentre.y;
            for(i=1;i<100;i++){
                LineEnd.x = VertexCentre.x+(((ADEnd.x-VertexCentre.x)*i)/100);
                LineEnd.y = VertexCentre.y + ((((float)100-slew_profiles[1][7][i])*(float)(ADEnd.y-VertexCentre.y))/100);
                DrawLineEx(LineStart,LineEnd,1,BLACK);
                LineStart.x = LineEnd.x;
                LineStart.y = LineEnd.y;
            }
            //Make sure the line actually arrives at the endpoint
            DrawLineEx(LineStart,ADEnd,1,BLACK);

            //Draw the end Vertex
            DrawRectangleLines(ADEnd.x-4,ADEnd.y-4,8,8,BLACK);
            
            
        
        }
    }
    // Handle any screen overlays - these need to 
    // be added within the Drawing loop
    ShowScreenOverlays();
    EndDrawing();
}

/* gui_SingleADSR displays & edits the ADSR profile for 
 * a track of type SingleADSR
 */
void gui_SingleADSR(void){
    int track;
    
    BeginDrawing();
    DrawTexture(MainScreenTexture,0,0,WHITE);
    for (track = 0; track < MAX_TRACKS; track++){
        if (Europi.tracks[track].selected == TRUE){

            DrawText("Track type ADSR",30,100,20,DARKGRAY);
        
        }
    }
    // Handle any screen overlays - these need to 
    // be added within the Drawing loop
    ShowScreenOverlays();
    EndDrawing();
}

/*
 * gui_SingleChannel displays just the currently
 * selected channel on a page of its own
 */
void gui_SingleChannel_old2(void){
    int track;
    int step;
    int val;
    char track_no[20];
    int row;
    Rectangle stepRectangle = {0,0,0,0};
    BeginDrawing();
    DrawTexture(MainScreenTexture,0,0,WHITE);
    for (track = 0; track < MAX_TRACKS; track++){
        if (Europi.tracks[track].selected == TRUE){
            sprintf(track_no,"%d",track+1);
            for (step = 0; step < MAX_STEPS; step++){
                row = step / 16;
                if(step < Europi.tracks[track].last_step){
                    int Octave = (int)((float)Europi.tracks[track].channels[CV_OUT].steps[step].scaled_value / (float)6000);
                    val = (int)(((float)Europi.tracks[track].channels[CV_OUT].steps[step].scaled_value - (Octave * 6000)) / (float)60);
                    stepRectangle.x = ((step-(row*16)) * 18)+20;
                    stepRectangle.y = ((row+1) * 100)-val;
                    /* Width of the bar is the Octave */
                    stepRectangle.width = Octave+5;
                    stepRectangle.height = val;
                    if(step == Europi.tracks[track].current_step){
                        DrawRectangleRec(stepRectangle,MAROON);
                    }
                    else{
                        DrawRectangleRec(stepRectangle,LIME);
                    }
/*                    // Gate State
                    if (Europi.tracks[track].channels[GATE_OUT].steps[step].gate_value == 1){
                        sprintf(track_no,"%d",Europi.tracks[track].channels[GATE_OUT].steps[step].retrigger);
                        DrawText(track_no,15 + (step*9),220,10,DARKGRAY);
                    }
                    // Slew
                    if (Europi.tracks[track].channels[CV_OUT].steps[step].slew_type != Off){
                        switch (Europi.tracks[track].channels[CV_OUT].steps[step].slew_shape){
                            case Both:
                                DrawText("V",15 + (step*9),230,10,DARKGRAY);
                            break;
                            case Rising:
                                DrawText("/",15 + (step*9),230,10,DARKGRAY);
                            break;
                            case Falling:
                                DrawText("\\",15 + (step*9),230,10,DARKGRAY);
                            break;
                        }
                    } */
                }
                /* Draws a block to show the last step (provided it's less than MAX_STEPS) */
                if(step == Europi.tracks[track].last_step - 1) {
                    val = (int)(((float)Europi.tracks[track].channels[CV_OUT].steps[step].scaled_value / (float)10000) * 100);
                    stepRectangle.x += 18;
                    stepRectangle.y = ((row+1) * 100)-val;
                    stepRectangle.width = 5;
                    stepRectangle.height = val;
                    DrawRectangleRec(stepRectangle,BLACK);
                }
            }
        }
    }
    // Handle any screen overlays - these need to 
    // be added within the Drawing loop
    ShowScreenOverlays();
    EndDrawing();
}

void gui_SingleChannel_old1(void){
    int track;
    int step;
    int val;
    char track_no[20];
    int row;
    Rectangle stepRectangle = {0,0,0,0};
    BeginDrawing();
    DrawTexture(MainScreenTexture,0,0,WHITE);
    for (track = 0; track < MAX_TRACKS; track++){
        if (Europi.tracks[track].selected == TRUE){
            sprintf(track_no,"%d",track+1);
            for (step = 0; step < MAX_STEPS; step++){
                row = step / 16;
                if(step < Europi.tracks[track].last_step){
                    //val = (int)(((float)Europi.tracks[track].channels[CV_OUT].steps[step].scaled_value / (float)60000) * 55);
                    val = (int)(((float)Europi.tracks[track].channels[CV_OUT].steps[step].scaled_value / (float)10000) * 100);
                    stepRectangle.x = ((step-(row*16)) * 18)+20;
                    stepRectangle.y = ((row+1) * 100)-val;
                    stepRectangle.width = 15;
                    stepRectangle.height = val;
                    if(step == Europi.tracks[track].current_step){
                        DrawRectangleRec(stepRectangle,MAROON);
                    }
                    else{
                        DrawRectangleRec(stepRectangle,LIME);
                    }
/*                    // Gate State
                    if (Europi.tracks[track].channels[GATE_OUT].steps[step].gate_value == 1){
                        sprintf(track_no,"%d",Europi.tracks[track].channels[GATE_OUT].steps[step].retrigger);
                        DrawText(track_no,15 + (step*9),220,10,DARKGRAY);
                    }
                    // Slew
                    if (Europi.tracks[track].channels[CV_OUT].steps[step].slew_type != Off){
                        switch (Europi.tracks[track].channels[CV_OUT].steps[step].slew_shape){
                            case Both:
                                DrawText("V",15 + (step*9),230,10,DARKGRAY);
                            break;
                            case Rising:
                                DrawText("/",15 + (step*9),230,10,DARKGRAY);
                            break;
                            case Falling:
                                DrawText("\\",15 + (step*9),230,10,DARKGRAY);
                            break;
                        }
                    } */
                }
            }
        }
    }
    // Handle any screen overlays - these need to 
    // be added within the Drawing loop
    ShowScreenOverlays();
    EndDrawing();
}

void gui_SingleChannel_Old(void){
    int track;
    int step;
    int val;
    char track_no[20];
    int txt_len;
    Rectangle stepRectangle = {0,0,0,0};
    BeginDrawing();
    ClearBackground(RAYWHITE);
    for (track = 0; track < MAX_TRACKS; track++){
        if (Europi.tracks[track].selected == TRUE){
            sprintf(track_no,"%d",track+1);
            txt_len = MeasureText(track_no,10);
            DrawText(track_no,12-txt_len,220,10,DARKGRAY);
            for (step = 0; step < MAX_STEPS; step++){
                if(step < Europi.tracks[track].last_step){
                    val = (int)(((float)Europi.tracks[track].channels[CV_OUT].steps[step].scaled_value / (float)60000) * 220);
                    if(step == Europi.tracks[track].current_step){
                        DrawRectangle(15 + (step*9),220-val,8,val,MAROON);
                    }
                    else{
                        DrawRectangle(15 + (step*9),220-val,8,val,LIME);
                    }
                    // Gate State
                    if (Europi.tracks[track].channels[GATE_OUT].steps[step].gate_type != Gate_Off){
                        sprintf(track_no,"%d",Europi.tracks[track].channels[GATE_OUT].steps[step].repetitions);
                        DrawText(track_no,15 + (step*9),220,10,DARKGRAY);
                    }
                    // Slew
                    if (Europi.tracks[track].channels[CV_OUT].steps[step].slew_type != Off){
                        switch (Europi.tracks[track].channels[CV_OUT].steps[step].slew_shape){
                            case Both:
                                DrawText("V",15 + (step*9),230,10,DARKGRAY);
                            break;
                            case Rising:
                                DrawText("/",15 + (step*9),230,10,DARKGRAY);
                            break;
                            case Falling:
                                DrawText("\\",15 + (step*9),230,10,DARKGRAY);
                            break;
                        }
                    }
                }
            }
        }
    }
    // Handle any screen overlays - these need to 
    // be added within the Drawing loop
    ShowScreenOverlays();
    EndDrawing();
}

/*
 * GUI_GRID Displays a grid of 32 steps by 21 channels - a bit
 * dense, but an interesting experiment in displaying a lot of
 * data on a small screen
 */
void gui_grid(void){
    Rectangle stepRectangle = {0,0,0,0};
    Rectangle trackRectangle = {0,0,0,0};
    int start_track,track, column;
    int step, offset, txt_len;
    char txt[20]; 
    /* Depending on the total number of tracks, and the position 
     * of the vertical scroll bar, the starting track will vary
     */
    if(last_track > 21){
        start_track = ((last_track-21) * VerticalScrollPercent) / 100;
        /* Don't display the Vertical Scroll Bar in certain situations */
        if(ActiveOverlays & ovl_Keyboard) { 
			ActiveOverlays &= ~ovl_VerticalScrollBar;
        }
        else {
            ActiveOverlays |= ovl_VerticalScrollBar;
        }
    }
    else {
        start_track = 0;
        ActiveOverlays &= ~ovl_VerticalScrollBar;
    }
    BeginDrawing();
    DrawTexture(MainScreenTexture,0,0,WHITE);
	int vOffset = 7;
	if(ShortScroll()) vOffset=29;
    char track_no[20];
    for(track=0;track<21;track++){
        // Track Number
        sprintf(track_no,"%d",start_track+track+1);
        txt_len = MeasureText(track_no,10);
        DrawText(track_no,17-txt_len,vOffset+(track * 10),10,DARKGRAY);
        // Check for Track select
        trackRectangle.x = 5;
        trackRectangle.y = vOffset+(track * 10);
        trackRectangle.width = 13;
        trackRectangle.height = 9;
 		if (CheckCollisionPointRec(touchPosition, trackRectangle) && (currentGesture != GESTURE_NONE)){
			if(OverlayActive( ovl_VerticalScrollBar ) == 0){
                // Open this track in a Single Channel view
                edit_track = start_track+track;
                select_track(start_track+track);
                ClearScreenOverlays();
                SwitchChannelFunction(edit_track);
				encoder_focus = track_select;
            }
			else {
				// Just update the selected track
				select_track(start_track+track);
				encoder_focus = track_select;
			}
        }
       
        for(step=0;step<32;step++){
            stepRectangle.x = 19+(step * 9);
            stepRectangle.y = vOffset+(track*10);
            stepRectangle.width = 8;
            stepRectangle.height = 9;
            // Check gesture collision (provided it's not beyond the last step of the track)
			if (CheckCollisionPointRec(touchPosition, stepRectangle) && (currentGesture == GESTURE_TAP) && (step < Europi.tracks[track].last_step) && (OverlayActive(ovl_VerticalScrollBar) == 0)){
                // Toggle Gate
                // To Do - this only toggles between Gate_Off and 50% gate - what we really
                // need is for the step structure to include a Gate On/Off switch, and for the gate
                // type to still be preserved 
                if (Europi.tracks[start_track+track].channels[GATE_OUT].steps[step].gate_type != Gate_Off){
                    Europi.tracks[start_track+track].channels[GATE_OUT].steps[step].gate_type = Gate_Off;
                 }
                 else {
                    Europi.tracks[start_track+track].channels[GATE_OUT].steps[step].gate_type = Gate_50;
                }
            }
            else if (CheckCollisionPointRec(touchPosition, stepRectangle) && (currentGesture == GESTURE_TAP) && (step == Europi.tracks[track].last_step) && (OverlayActive(ovl_VerticalScrollBar) == 0)){
                // Tap on last step - selects it for moving
                if(Europi.tracks[start_track+track].selected == TRUE){
                    // If it already selected, a second tap de-selects it
                    Europi.tracks[start_track+track].selected = FALSE;
                }
                else {
                    select_track(start_track+track);
                    selected_step = step;
                }
            }
            else if ((Europi.tracks[start_track+track].selected == TRUE) && (CheckCollisionPointRec(touchPosition, stepRectangle)) && (Europi.tracks[track].last_step == selected_step) && (currentGesture == GESTURE_HOLD) && (OverlayActive(ovl_VerticalScrollBar) == 0)){
                // If last step on this track is selected, and current gesture is
                // GESTURE_HOLD, then move the Last step to the current step
                Europi.tracks[start_track+track].last_step = step;
                selected_step = step;
            }
            if(step == Europi.tracks[start_track+track].last_step){
                // Paint last step
                if((step == selected_step) && (Europi.tracks[start_track+track].selected == TRUE)){
                    // If the last step on this track is selected for moving,
                    // colour it yellow
                    DrawRectangleRec(stepRectangle,YELLOW);
                }
                else {
                    DrawRectangleRec(stepRectangle, BLACK);
                }
            }
            else if(step > Europi.tracks[start_track+track].last_step){
                // Anything beyond the last step is greyed out
                DrawRectangleRec(stepRectangle, LIGHTGRAY);
            }
            else {
                // paint this step
                if (Europi.tracks[start_track+track].channels[GATE_OUT].steps[step].gate_type != Gate_Off){
                    // Some sort of gate
                    if(step == Europi.tracks[start_track+track].current_step){
                        DrawRectangleRec(stepRectangle,RED);
                        DrawRectangleLinesEx(stepRectangle,1,DARKGRAY);
                    }
                    else{
                        DrawRectangleRec(stepRectangle,MAROON);
                    }
                }
                else {
                    // Blank step (no gate)
                    if(step == Europi.tracks[start_track+track].current_step){
                        DrawRectangleRec(stepRectangle,WHITE);
                        DrawRectangleLinesEx(stepRectangle,1,DARKGRAY);
                    }
                    else {
                        DrawRectangleRec(stepRectangle,WHITE);
                    }
                }
            }
            // Draw demarcation lines after each multiple of 8 steps
            if((step == 7) || (step == 15) || (step == 23)){
                DrawLine(stepRectangle.x+stepRectangle.width+1,stepRectangle.y - 1,stepRectangle.x+stepRectangle.width+1,stepRectangle.y+stepRectangle.height,DARKGRAY);
            }
        }
    } 
    // Handle any screen overlays - these need to 
    // be added within the Drawing loop
    ShowScreenOverlays();
    EndDrawing();
}
/*
 * ShowScreenOverlays is called from within the 
 * drawing loop of each main type of display
 * page, and enables Menus, user input controls
 * etc to be overlayed on top of the currently
 * displayed page
 */
void ShowScreenOverlays(void){
    gui_debug();
    if(ActiveOverlays & ovl_MainMenu){
        gui_MainMenu();
    }
    if(ActiveOverlays & ovl_BPM){
        char strBPM[10];
        sprintf(strBPM,"%02d BPM",clock_freq);
        DrawTexture(SmallDialogTexture,157,180,WHITE);
        DrawText(strBPM,167,188,20,DARKGRAY);
    }

    if(ActiveOverlays & ovl_ModalDialog){
        DrawTexture(TopBarTexture,0,0,WHITE);
        DrawRectangle(5,28, 309, 184, CLR_LIGHTBLUE);
        int txt_len = MeasureText(modal_dialog_txt1,20);
        DrawText(modal_dialog_txt1,158-(txt_len/2),80,20,DARKGRAY);
        txt_len = MeasureText(modal_dialog_txt2,20);
        DrawText(modal_dialog_txt2,158-(txt_len/2),100,20,DARKGRAY);
        txt_len = MeasureText(modal_dialog_txt3,20);
        DrawText(modal_dialog_txt3,158-(txt_len/2),120,20,DARKGRAY);
        txt_len = MeasureText(modal_dialog_txt4,20);
        DrawText(modal_dialog_txt4,158-(txt_len/2),140,20,DARKGRAY);
        
    }
    if(ActiveOverlays & ovl_SetZero){
        int track = 0;
        char str[80];
        char strTrack[5];
        char strZero[5];
        DrawTexture(TopBarTexture,0,0,WHITE);
        DrawTexture(Text2chTexture,70,2,WHITE); // Box for Track Number
        DrawTexture(Text5chTexture,210,2,WHITE);// Box for Zero value
        DrawText("Track",5,5,20,DARKGRAY);
        DrawText("Zero Val",112,5,20,DARKGRAY);
        // Check for Tap within Track or Value boxes, and set 
		// focus accordingly
		Rectangle touchRectangle = {71,3,30,22};
		if (CheckCollisionPointRec(touchPosition, touchRectangle) && (currentGesture == GESTURE_TAP)){
			encoder_focus = track_select;
		}
		touchRectangle.x = 210;
		touchRectangle.y = 3;
		touchRectangle.width = 67;
		touchRectangle.height = 22;
		if (CheckCollisionPointRec(touchPosition, touchRectangle) && (currentGesture == GESTURE_TAP)){
			encoder_focus = set_zerolevel;
		}
		
        for(track = 0; track < MAX_TRACKS; track++) {
            if (Europi.tracks[track].selected == TRUE){
                sprintf(strTrack,"%02d",track+1);
                sprintf(strZero,"%05d",Europi.tracks[track].channels[CV_OUT].scale_zero);
                DrawText(strTrack,75,5,20,DARKGRAY);
                DrawText(strZero,215,5,20,DARKGRAY);
                if(encoder_focus == track_select){
                    DrawRectangleLines(71,3,30,22,RED);
                    DrawRectangleLines(72,4,28,20,RED);
                }
                else if (encoder_focus == set_zerolevel) {
                    DrawRectangleLines(210,3,67,22,RED);
                    DrawRectangleLines(211,4,65,20,RED);
                }
            }
        }
        // Check for Select button
        if (btnA_state == 1){
            btnA_state = 0;
            if(encoder_focus == track_select) encoder_focus = set_zerolevel;
            else encoder_focus = track_select;
        }
        if (btnB_state == 1){
            // Check for Val -
            btnB_state = 0;
            if(encoder_focus == track_select) select_next_track(DOWN);
            //else set_loop_point(DOWN);
        }
        if (btnC_state == 1){
            // Check for Val +
            btnC_state = 0;
            if(encoder_focus == track_select) select_next_track(UP);
            //else set_loop_point(UP);
        }
    }
    if(ActiveOverlays & ovl_SetTen){
        int track = 0;
        char str[80];
        char strTrack[5];
        char strMax[5];
        DrawTexture(TopBarTexture,0,0,WHITE);
        DrawTexture(Text2chTexture,70,2,WHITE); // Box for Track Number
        DrawTexture(Text5chTexture,210,2,WHITE);// Box for Zero value
        DrawText("Track",5,5,20,DARKGRAY);
        DrawText("10v Value",112,5,20,DARKGRAY);
        // Check for Tap within Track or Value boxes, and set 
		// focus accordingly
		Rectangle touchRectangle = {71,3,30,22};
		if (CheckCollisionPointRec(touchPosition, touchRectangle) && (currentGesture == GESTURE_TAP)){
			encoder_focus = track_select;
		}
		touchRectangle.x = 210;
		touchRectangle.y = 3;
		touchRectangle.width = 67;
		touchRectangle.height = 22;
		if (CheckCollisionPointRec(touchPosition, touchRectangle) && (currentGesture == GESTURE_TAP)){
			encoder_focus = set_maxlevel;
		}
        
        for(track = 0; track < MAX_TRACKS; track++) {
            if (Europi.tracks[track].selected == TRUE){
                sprintf(strTrack,"%02d",track+1);
                sprintf(strMax,"%05d",Europi.tracks[track].channels[CV_OUT].scale_max);
                DrawText(strTrack,75,5,20,DARKGRAY);
                DrawText(strMax,215,5,20,DARKGRAY);
                if(encoder_focus == track_select){
                    DrawRectangleLines(71,3,30,22,RED);
                    DrawRectangleLines(72,4,28,20,RED);
                }
                else if (encoder_focus == set_maxlevel) {
                    DrawRectangleLines(210,3,67,22,RED);
                    DrawRectangleLines(211,4,65,20,RED);
                }
            }
        }
        // Check for Select button
        if (btnA_state == 1){
            btnA_state = 0;
            if(encoder_focus == track_select) encoder_focus = set_maxlevel;
            else encoder_focus = track_select;
        }
        if (btnB_state == 1){
            // Check for Val -
            btnB_state = 0;
            if(encoder_focus == track_select) select_next_track(DOWN);
        }
        if (btnC_state == 1){
            // Check for Val +
            btnC_state = 0;
            if(encoder_focus == track_select) select_next_track(UP);
        }
    }
    if(ActiveOverlays & ovl_SetLoop){
        int track = 0;
        char str[80];
        char strTrack[5];
        char strLoop[5];
        DrawTexture(TopBarTexture,0,0,WHITE);
        DrawTexture(Text2chTexture,70,2,WHITE); // Box for Track Number
        DrawTexture(Text2chTexture,185,2,WHITE); // Box for Step Number
        DrawText("Track",5,5,20,DARKGRAY);
        DrawText("Length",112,5,20,DARKGRAY);
        // Check for Tap within Track or Value boxes, and set 
		// focus accordingly
		Rectangle touchRectangle = {71,3,30,22};
		if (CheckCollisionPointRec(touchPosition, touchRectangle) && (currentGesture == GESTURE_TAP)){
			encoder_focus = track_select;
		}
		touchRectangle.x = 186;
		touchRectangle.y = 3;
		touchRectangle.width = 30;
		touchRectangle.height = 22;
		if (CheckCollisionPointRec(touchPosition, touchRectangle) && (currentGesture == GESTURE_TAP)){
			encoder_focus = set_loop;
		}
        
        for(track = 0; track < MAX_TRACKS; track++) {
            if (Europi.tracks[track].selected == TRUE){
                sprintf(strTrack,"%02d",track+1);
                sprintf(strLoop,"%02d",Europi.tracks[track].last_step);
                DrawText(strTrack,75,5,20,DARKGRAY);
                DrawText(strLoop,190,5,20,DARKGRAY);
                if(encoder_focus == track_select){
                    DrawRectangleLines(71,3,30,22,RED);
                    DrawRectangleLines(72,4,28,20,RED);
                }
                else if (encoder_focus == set_loop) {
                    DrawRectangleLines(186,3,30,22,RED);
                    DrawRectangleLines(187,4,28,20,RED);
                }
            }
        }
        // Check for Select button
        if (btnA_state == 1){
            btnA_state = 0;
            if(encoder_focus == track_select) encoder_focus = set_loop;
            else encoder_focus = track_select;
        }
        if (btnB_state == 1){
            // Check for Val -
            btnB_state = 0;
            if(encoder_focus == track_select) select_next_track(DOWN);
            else set_loop_point(DOWN);
        }
        if (btnC_state == 1){
            // Check for Val +
            btnC_state = 0;
            if(encoder_focus == track_select) select_next_track(UP);
            else set_loop_point(UP);
        }

    }
    if(ActiveOverlays & ovl_SetSlew){
        //TODO: This isn't finished yet, and probably needs a 
        //double-height control panel to get all the detail in 
        int track = 0;
        char strTrack[5];
        char strStep[5];
        char strSlew[9];
        DrawTexture(TopBarTexture,0,0,WHITE);
        DrawTexture(Text2chTexture,45,2,WHITE); // Box for Track Number
        DrawTexture(Text2chTexture,135,2,WHITE); // Box for Step Number
        DrawTexture(Text10chTexture,222,2,WHITE); // Box for Slew Value
        Rectangle touchRectangle = {46,3,30,22};
		if (CheckCollisionPointRec(touchPosition, touchRectangle) && (currentGesture == GESTURE_TAP)){
			encoder_focus = track_select;
		}
        touchRectangle.x = 136;
        touchRectangle.y = 3;
        touchRectangle.width = 30;
        touchRectangle.height = 22;
        if (CheckCollisionPointRec(touchPosition, touchRectangle) && (currentGesture == GESTURE_TAP)){
			encoder_focus = step_select;
		}
        touchRectangle.x = 223;
        touchRectangle.y = 3;
        touchRectangle.width = 87;
        touchRectangle.height = 22;
        if (CheckCollisionPointRec(touchPosition, touchRectangle) && (currentGesture == GESTURE_TAP)){
			encoder_focus = slew_type;
		}

        DrawText("Trk",5,5,20,DARKGRAY);
        DrawText("Step",85,5,20,DARKGRAY);         // was 105
        DrawText("Slew",175,5,20,DARKGRAY);
        
        for(track = 0; track < MAX_TRACKS; track++) {
            if (Europi.tracks[track].selected == TRUE){
                sprintf(strTrack,"%02d",track+1);
                sprintf(strStep,"%02d",Europi.tracks[track].current_step+1);
                switch (Europi.tracks[track].channels[CV_OUT].steps[Europi.tracks[track].current_step].slew_type){
                    default:
                    case Off:
                        DrawText("Off",228,5,20,DARKGRAY);
                    break;
                    case Linear:
                        DrawText("Lin",228,5,20,DARKGRAY);
                    break;
                    case Exponential:
                        DrawText("Exp",228,5,20,DARKGRAY);
                    break;
                    case RevExp:
                        DrawText("RevExp",228,5,20,DARKGRAY);
                    break;
                    case Log:
                        DrawText("Log",228,5,20,DARKGRAY);
                    break;
                    case RevLog:
                        DrawText("RevLog",228,5,20,DARKGRAY);
                    break;
                    case Sine:
                        DrawText("Sine",228,5,20,DARKGRAY);
                    break;
                    case RevSine:
                        DrawText("RevSine",228,5,20,DARKGRAY);
                    break;
                    case Cosine:
                        DrawText("Cosine",228,5,20,DARKGRAY);
                    break;
                    
                }

                DrawText(strTrack,50,5,20,DARKGRAY);
                DrawText(strStep,140,5,20,DARKGRAY);
                if(encoder_focus == track_select){
                    DrawRectangleLines(46,3,30,22,RED);
                    DrawRectangleLines(47,4,28,20,RED);
                }
                else if (encoder_focus == step_select) {
                    DrawRectangleLines(136,3,30,22,RED);
                    DrawRectangleLines(137,4,28,20,RED);
                }
                else if (encoder_focus == slew_type){
                    DrawRectangleLines(223,3,87,22,RED);
                    DrawRectangleLines(224,4,85,20,RED);
                }
            }
        }
        // Check for Select button
        if (btnA_state == 1){
            btnA_state = 0;
            if(encoder_focus == track_select) encoder_focus = step_select;
            else if(encoder_focus == step_select) encoder_focus = slew_type;
            else encoder_focus = track_select;
        }
        if (btnB_state == 1){
            // Check for Val -
            btnB_state = 0;
            if(encoder_focus == track_select) select_next_track(DOWN);
            else if(encoder_focus == step_select) select_next_step(DOWN); 
            else select_next_slew(DOWN);
        }
        if (btnC_state == 1){
            // Check for Val +
            btnC_state = 0;
            if(encoder_focus == track_select) select_next_track(UP);
            else if(encoder_focus == step_select) select_next_step(UP); 
            else select_next_slew(UP);
        }

    }
    if(ActiveOverlays & ovl_SetPitch){ 
        int track = 0;
        char strTrack[5];
        char strStep[5];
        char strPitch[9];
        DrawTexture(TopBarTexture,0,0,WHITE);
        DrawTexture(Text2chTexture,70,2,WHITE); // Box for Track Number
        DrawTexture(Text2chTexture,155,2,WHITE); // Box for Step Number
        DrawTexture(Text5chTexture,245,2,WHITE); // Box for Pitch Value
        Rectangle touchRectangle = {71,3,30,22};
		if (CheckCollisionPointRec(touchPosition, touchRectangle) && (currentGesture == GESTURE_TAP)){
			encoder_focus = track_select;
		}
        touchRectangle.x = 156;
        touchRectangle.y = 3;
        touchRectangle.width = 30;
        touchRectangle.height = 22;
        if (CheckCollisionPointRec(touchPosition, touchRectangle) && (currentGesture == GESTURE_TAP)){
			encoder_focus = step_select;
		}
        touchRectangle.x = 246;
        touchRectangle.y = 3;
        touchRectangle.width = 66;
        touchRectangle.height = 22;
        if (CheckCollisionPointRec(touchPosition, touchRectangle) && (currentGesture == GESTURE_TAP)){
			encoder_focus = set_pitch;
		}

        DrawText("Track",5,5,20,DARKGRAY);
        DrawText("Step",105,5,20,DARKGRAY);
        DrawText("Pitch",190,5,20,DARKGRAY);
        for(track = 0; track < MAX_TRACKS; track++) {
            if (Europi.tracks[track].selected == TRUE){
                sprintf(strTrack,"%02d",track+1);
                sprintf(strStep,"%02d",Europi.tracks[track].current_step+1);
                sprintf(strPitch,"%05d",Europi.tracks[track].channels[CV_OUT].steps[Europi.tracks[track].current_step].raw_value);
                DrawText(strTrack,75,5,20,DARKGRAY);
                DrawText(strStep,160,5,20,DARKGRAY);
                DrawText(strPitch,250,5,20,DARKGRAY);
                if(encoder_focus == track_select){
                    DrawRectangleLines(71,3,30,22,RED);
                    DrawRectangleLines(72,4,28,20,RED);
                }
                else if (encoder_focus == step_select) {
                    DrawRectangleLines(156,3,30,22,RED);
                    DrawRectangleLines(157,4,28,20,RED);
                }
                else if (encoder_focus == set_pitch){
                    DrawRectangleLines(246,3,66,22,RED);
                    DrawRectangleLines(247,4,64,20,RED);
                }
            }
        }
         // Check for Select button
        if (btnA_state == 1){
            btnA_state = 0;
            switch(encoder_focus){
                case track_select:
                    encoder_focus = step_select;
                break;
                case step_select:
                    encoder_focus = set_pitch;
                break;
                case set_pitch:
                default:
                    encoder_focus = track_select;
                break;
            }
        }
        if (btnB_state == 1){
            // Check for Val -
            btnB_state = 0;
            switch(encoder_focus){
                case track_select:
                    select_next_track(DOWN);
                break;
                case step_select:
                    select_next_step(DOWN);
                break;
                case set_pitch:
                    set_step_pitch(DOWN,1);  // no velocity available
                break;
                default:
                break;
            }
        }
        if (btnC_state == 1){
            // Check for Val +
            btnC_state = 0;
            switch(encoder_focus){
                case track_select:
                    select_next_track(UP);
                break;
                case step_select:
                    select_next_step(UP);
                break;
                case set_pitch:
                    set_step_pitch(UP,1);  // no velocity availab~ovl_BPM
            }
        }
       
    }
    if(ActiveOverlays & ovl_SetQuantise){
        int track = 0;
        char str[80];
        char strTrack[5];
        char strScale[30];
        DrawTexture(TopBarTexture,0,0,WHITE);
        DrawTexture(Text2chTexture,70,2,WHITE); 
        DrawTexture(TextInputTexture,103,2,WHITE);
        DrawText("Track",5,5,20,DARKGRAY);
		// Check for Tap within Track or Value boxes, and set 
		// focus accordingly
		Rectangle touchRectangle = {71,3,30,22};
		if (CheckCollisionPointRec(touchPosition, touchRectangle) && (currentGesture == GESTURE_TAP)){
			encoder_focus = track_select;
		}
		touchRectangle.x = 103;
		touchRectangle.y = 3;
		touchRectangle.width = 213;
		touchRectangle.height = 22;
		if (CheckCollisionPointRec(touchPosition, touchRectangle) && (currentGesture == GESTURE_TAP)){
			encoder_focus = set_quantise;
		}
 
        for(track = 0; track < MAX_TRACKS; track++) {
            if (Europi.tracks[track].selected == TRUE){
                sprintf(strTrack,"%02d",track+1);
                sprintf(strScale,"%s",scale_names[Europi.tracks[track].channels[CV_OUT].quantise]);
                DrawText(strTrack,75,5,20,DARKGRAY);
                DrawText(strScale,110,5,20,DARKGRAY);
                if(encoder_focus == track_select){
                    DrawRectangleLines(71,3,30,22,RED);
                    DrawRectangleLines(72,4,28,20,RED);
                }
                else if (encoder_focus == set_quantise) {
                    DrawRectangleLines(103,3,213,22,RED);
                    DrawRectangleLines(104,4,211,20,RED);

                }
            }
        }
        // Check for Select button
        if (btnA_state == 1){
            btnA_state = 0;
            if(encoder_focus == track_select) encoder_focus = set_quantise;
            else encoder_focus = track_select;
        }
        if (btnB_state == 1){
            // Check for Val -
            btnB_state = 0;
            if(encoder_focus == track_select) select_next_track(DOWN);
            else select_next_quantisation(DOWN);
        }
        if (btnC_state == 1){
            // Check for Val +
            btnC_state = 0;
            if(encoder_focus == track_select) select_next_track(UP);
            else select_next_quantisation(UP);
        }
 
   }

    if(ActiveOverlays & ovl_SetDirection){   // track Direction
        int track = 0;
        char str[80];
        char strTrack[5];
        char strDirection[20];
        DrawTexture(TopBarTexture,0,0,WHITE);
        DrawTexture(Text2chTexture,70,2,WHITE); 
        DrawTexture(TextInputTexture,103,2,WHITE);
        DrawText("Track",5,5,20,DARKGRAY);
		// Check for Tap within Track or Value boxes, and set 
		// focus accordingly
		Rectangle touchRectangle = {71,3,30,22};
		if (CheckCollisionPointRec(touchPosition, touchRectangle) && (currentGesture == GESTURE_TAP)){
			encoder_focus = track_select;
		}
		touchRectangle.x = 103;
		touchRectangle.y = 3;
		touchRectangle.width = 213;
		touchRectangle.height = 22;
		if (CheckCollisionPointRec(touchPosition, touchRectangle) && (currentGesture == GESTURE_TAP)){
			encoder_focus = set_direction;
		}

        for(track = 0; track < MAX_TRACKS; track++) {
            if (Europi.tracks[track].selected == TRUE){
                sprintf(strTrack,"%02d",track+1);
                DrawText(strTrack,75,5,20,DARKGRAY);
                switch (Europi.tracks[track].direction){
                    default:
                    case Forwards:
                        DrawText("Forwards",110,5,20,DARKGRAY);
                    break;
                    case Backwards:
                        DrawText("Backwards",110,5,20,DARKGRAY);
                    break;
                    case Pendulum_F:
                    case Pendulum_B:
                        DrawText("Pendulum",110,5,20,DARKGRAY);
                    break;
                    case Random:
                        DrawText("Random",110,5,20,DARKGRAY);
                    break;
                    
                }
                if(encoder_focus == track_select){
                    DrawRectangleLines(71,3,30,22,RED);
                    DrawRectangleLines(72,4,28,20,RED);
                }
                else if(encoder_focus == set_direction){
                    DrawRectangleLines(103,3,213,22,RED);
                    DrawRectangleLines(104,4,211,20,RED);
                }
            }
        }
        // Check for Select button
        if (btnA_state == 1){
            btnA_state = 0;
            if(encoder_focus == track_select) encoder_focus = set_direction;
            else encoder_focus = track_select;
        }
        if (btnB_state == 1){
            // Check for Val -
            btnB_state = 0;
            if(encoder_focus == track_select) select_next_track(DOWN);
            else select_next_direction(DOWN);
        }
        if (btnC_state == 1){
            // Check for Val +
            btnC_state = 0;
            if(encoder_focus == track_select) select_next_track(UP);
            else select_next_direction(UP);
        }
 
   }

    
    
    if(ActiveOverlays & ovl_Keyboard){
        Rectangle btnHighlight = {0,0,0,0};
        int button;
        int row, col;
        DrawTexture(KeyboardTexture,KBD_GRID_TL_X,KBD_GRID_TL_Y,WHITE);
        for(button=0;button < (KBD_ROWS * KBD_COLS);button++){
            row = button / KBD_COLS;
            col = button % KBD_COLS;
            btnHighlight.x = (KBD_GRID_TL_X + KBD_BTN_TL_X) + (col * KBD_COL_WIDTH);
            btnHighlight.y = (KBD_GRID_TL_Y + KBD_BTN_TL_Y) + (row * KBD_ROW_HEIGHT);
            btnHighlight.width = KBD_BTN_WIDTH;
            btnHighlight.height = KBD_BTN_HEIGHT;
            if(button == kbd_char_selected){
                //Highlight this button
                DrawRectangleLines((KBD_GRID_TL_X + KBD_BTN_TL_X) + (col * KBD_COL_WIDTH),
                (KBD_GRID_TL_Y + KBD_BTN_TL_Y) + (row * KBD_ROW_HEIGHT),
                KBD_BTN_WIDTH,
                KBD_BTN_HEIGHT,WHITE);
            }
            // Check for touch input
            if (CheckCollisionPointRec(touchPosition, btnHighlight) && (currentGesture == GESTURE_TAP)){
                if(currentGesture != lastGesture){
                    kbd_char_selected = button;
                    row = button / KBD_COLS;
                    col = button % KBD_COLS;
                    //Add this to the input_txt buffer
					if(strcmp(kbd_chars[row][col],"~") == 0){
						// This is BackSpace
						if(strlen(input_txt) >= 1){
							input_txt[strlen(input_txt)-1] = '\0';
						}
					}
					else if(strcmp(kbd_chars[row][col],"]") == 0){
						btnB_state = 1;	// Simulate clicking OK
					}
					else  sprintf(input_txt,"%s%s", input_txt,kbd_chars[row][col]);
                }
            }
        }
    }
    if(ActiveOverlays & ovl_FileOpen){
        Rectangle fileHighlight = {0,0,0,0};
        DrawTexture(DialogTexture,0,0,WHITE);
        DrawText("File Open",10,5,20,DARKGRAY);
        // Calculate first fiile tto show based on scroll bar position
        if (file_count <= DLG_ROWS){
            first_file = 0;
        }
        else{
            first_file = ((file_count - DLG_ROWS) * VerticalScrollPercent) / 100;
        }
        // List the files
        int i;
        int j=0;
        for(i=0;i<file_count;i++){
            if((i >= first_file) & (i < first_file + DLG_ROWS)){
                fileHighlight.x=5;
                fileHighlight.y=27+(j*20);
                fileHighlight.width=310;
                fileHighlight.height=20;
                // Check for touch input
                if (CheckCollisionPointRec(touchPosition, fileHighlight) && (currentGesture != GESTURE_NONE)){
                    file_selected = i;
                }

                if(i == file_selected) {
                    //highlight this file
                    DrawRectangleRec(fileHighlight,LIGHTGRAY);
                }
                DrawText(files[i],10,27+(j*20),20,DARKGRAY);
                j++;
            }
        }
        // Check for Open button
        if (btnB_state == 1){
            // Open Button Touched
            btnB_state = 0;
            //char filename[100]; 
            snprintf(current_filename, 100, "resources/sequences/%s", files[file_selected]);
            load_sequence(current_filename);
            ClearScreenOverlays();
            buttonsDefault();
            VerticalScrollPercent = 0;
        }
        if (btnC_state == 1){
            // Cancel Button Touched
            btnC_state = 0;
			ClearScreenOverlays();
            buttonsDefault();
        }
        
    }
    if(ActiveOverlays & ovl_FileSaveAs){
        // Top data entry bar
        DrawTexture(TopBarTexture,0,0,WHITE);
        DrawTexture(TextInputTexture,103,1,WHITE);
        DrawText("Save As:",10,MENU_TOP_MARGIN,20,DARKGRAY);
        DrawText(input_txt,110,4,20,DARKGRAY);
    }

    if(ActiveOverlays & ovl_VerticalScrollBar){
		// Check whether this is normal scroll bar or short one
		if(ShortScroll()) {
			// Short scroll bar
			DrawTexture(VerticalScrollBarShortTexture,303,27,WHITE);
			int ScrollHandlePosn = (((SHORT_VERTICAL_SCROLL_MAX-SHORT_VERTICAL_SCROLL_MIN) * VerticalScrollPercent) / 100) + SHORT_VERTICAL_SCROLL_MIN;
			DrawTexture(ScrollHandleTexture,304,ScrollHandlePosn,WHITE);
			// test rectangles for buttons
			Rectangle scrollUpButton = {303,26,13,15};
			Rectangle scrollDownButton = {303,198,13,15};
			Rectangle scrollHandleRec = {303,ScrollHandlePosn-2,14,15}; //note: setting the collision box a couple of pixels above the actual button makes it easier to drag upwards!!
			if (CheckCollisionPointRec(touchPosition, scrollUpButton) && (currentGesture != GESTURE_NONE)){
				DrawRectangleLines(304, 27, 12, 14, CLR_DARKBLUE);
				DrawRectangleLines(305, 28, 10, 12, CLR_DARKBLUE);
				if(VerticalScrollPercent >= 1) VerticalScrollPercent--;
			}
			if (CheckCollisionPointRec(touchPosition, scrollDownButton) && (currentGesture != GESTURE_NONE)){
				DrawRectangleLines(304, 199, 12, 14, CLR_DARKBLUE); 
				DrawRectangleLines(305, 200, 10, 12, CLR_DARKBLUE); 
				if(VerticalScrollPercent <= 99) VerticalScrollPercent++;
			}
			
			if (CheckCollisionPointRec(touchPosition, scrollHandleRec) && (currentGesture == GESTURE_DRAG)){
				DrawRectangleLines(303, ScrollHandlePosn, 14, 13, CLR_DARKBLUE);
				DrawRectangleLines(304, ScrollHandlePosn+1, 12, 11, CLR_DARKBLUE);
				if((touchPosition.y >= (float)SHORT_VERTICAL_SCROLL_MIN) && (touchPosition.y <= (float)SHORT_VERTICAL_SCROLL_MAX)) {
					VerticalScrollPercent = (int)(((touchPosition.y - (float)SHORT_VERTICAL_SCROLL_MIN) / (float)(SHORT_VERTICAL_SCROLL_MAX - SHORT_VERTICAL_SCROLL_MIN)) * 100);
				}
			}
		}
		else {
			// Tall vertical scroll bar on RHS of screen
			DrawTexture(VerticalScrollBarTexture,303,4,WHITE);
			int ScrollHandlePosn = (((VERTICAL_SCROLL_MAX-VERTICAL_SCROLL_MIN) * VerticalScrollPercent) / 100) + VERTICAL_SCROLL_MIN;
			DrawTexture(ScrollHandleTexture,304,ScrollHandlePosn,WHITE);
			// test rectangles for buttons
			Rectangle scrollUpButton = {303,4,13,15};
			Rectangle scrollDownButton = {303,198,13,15};
			Rectangle scrollHandleRec = {303,ScrollHandlePosn-2,14,15}; //note: setting the collision box a couple of pixels above the actual button makes it easier to drag upwards!!
			if (CheckCollisionPointRec(touchPosition, scrollUpButton) && (currentGesture != GESTURE_NONE)){
				DrawRectangleLines(304, 4, 12, 14, CLR_DARKBLUE);
				DrawRectangleLines(305, 5, 10, 12, CLR_DARKBLUE);
				if(VerticalScrollPercent >= 1) VerticalScrollPercent--;
			}
			if (CheckCollisionPointRec(touchPosition, scrollDownButton) && (currentGesture != GESTURE_NONE)){
				DrawRectangleLines(304, 199, 12, 14, CLR_DARKBLUE); 
				DrawRectangleLines(305, 200, 10, 12, CLR_DARKBLUE); 
				if(VerticalScrollPercent <= 99) VerticalScrollPercent++;
			}
			
			if (CheckCollisionPointRec(touchPosition, scrollHandleRec) && (currentGesture == GESTURE_DRAG)){
				DrawRectangleLines(303, ScrollHandlePosn, 14, 13, CLR_DARKBLUE);
				DrawRectangleLines(304, ScrollHandlePosn+1, 12, 11, CLR_DARKBLUE);
				if((touchPosition.y >= (float)VERTICAL_SCROLL_MIN) && (touchPosition.y <= (float)VERTICAL_SCROLL_MAX)) {
					VerticalScrollPercent = (int)(((touchPosition.y - (float)VERTICAL_SCROLL_MIN) / (float)(VERTICAL_SCROLL_MAX - VERTICAL_SCROLL_MIN)) * 100);
				}
			}
		}
    }
    if(ActiveOverlays & ovl_SingleStep){
            char strTrack[5];
            char strStep[5];
            DrawTexture(TopBarTexture,0,0,WHITE);
            DrawTexture(Text2chTexture,75,2,WHITE); // Box for Track Number
            DrawTexture(Text2chTexture,180,2,WHITE); // Box for Step Number
            DrawText("Track:",5,5,20,DARKGRAY);
            DrawText("Step:",125,5,20,DARKGRAY);
            sprintf(strTrack,"%02d",edit_track+1);
            sprintf(strStep,"%02d",edit_step+1);
            DrawText(strTrack,80,5,20,DARKGRAY);
            DrawText(strStep,185,5,20,DARKGRAY);
            if (btnB_state == 1){
                // Check for Prev
                btnB_state = 0;
                if(edit_step <= 0){
                    edit_step=Europi.tracks[edit_track].last_step-1;
                }
                else {
                    edit_step--;
                }
                // Set the display type for this new Track
                
            }
            if (btnC_state == 1){
                // Check for Next
                if(++edit_step >= Europi.tracks[edit_track].last_step){
                    edit_step=0;
                }
                btnC_state = 0;
            }

    }
    if(ActiveOverlays & ovl_SingleChannel){
        char strTrack[5];
        DrawTexture(TopBarTexture,0,0,WHITE);
        DrawTexture(Text2chTexture,75,2,WHITE); // Box for Track Number
        DrawText("Track:",5,5,20,DARKGRAY);
        sprintf(strTrack,"%02d",edit_track+1);
        DrawText(strTrack,80,5,20,DARKGRAY);
		if(encoder_focus == track_select){
			DrawRectangleLines(76,3,30,22,RED);
			DrawRectangleLines(77,4,28,20,RED);
		}

        if (btnB_state == 1){
            // Check for Prev
			btnB_state = 0;
			select_next_track(-1);
            SingleChannelOffset = 0;
            select_track(edit_track);
            SwitchChannelFunction(edit_track);
			encoder_focus = track_select;
        }
        if (btnC_state == 1){
            // Check for Next
            btnC_state = 0;
			select_next_track(1);
            SingleChannelOffset = 0;
            select_track(edit_track);
            SwitchChannelFunction(edit_track);
			encoder_focus = track_select;
        }
    }
    if(ActiveOverlays & ovl_SingleAD){
        char strTrack[5];
        DrawTexture(TopBarTexture,0,0,WHITE);
        DrawTexture(Text2chTexture,75,2,WHITE); // Box for Track Number
        DrawText("Track:",5,5,20,DARKGRAY);
        sprintf(strTrack,"%02d",edit_track+1);
        DrawText(strTrack,80,5,20,DARKGRAY);
        if (btnB_state == 1){
            // Check for Prev
            btnB_state = 0;
            if(edit_track <= 0){
                edit_track = last_track-1;
            }
            else {
                edit_track--;
            }
            SingleChannelOffset = 0;
            select_track(edit_track);
            SwitchChannelFunction(edit_track);
        }
        if (btnC_state == 1){
            // Check for Next
            if(++edit_track >= last_track){
                edit_track=0;
            }
            btnC_state = 0;
            SingleChannelOffset = 0;
            select_track(edit_track);
            SwitchChannelFunction(edit_track);
        }
    }
    if(ActiveOverlays & ovl_SingleADSR){
        char strTrack[5];
        DrawTexture(TopBarTexture,0,0,WHITE);
        DrawTexture(Text2chTexture,75,2,WHITE); // Box for Track Number
        DrawText("Track:",5,5,20,DARKGRAY);
        sprintf(strTrack,"%02d",edit_track+1);
        DrawText(strTrack,80,5,20,DARKGRAY);
        if (btnB_state == 1){
            // Check for Prev
            btnB_state = 0;
            if(edit_track <= 0){
                edit_track = last_track-1;
            }
            else {
                edit_track--;
            }
            SingleChannelOffset = 0;
            select_track(edit_track);
            SwitchChannelFunction(edit_track);
        }
        if (btnC_state == 1){
            // Check for Next
            if(++edit_track >= last_track){
                edit_track=0;
            }
            btnC_state = 0;
            SingleChannelOffset = 0;
            select_track(edit_track);
            SwitchChannelFunction(edit_track);
        }
    }
    // The soft button function bar is always displayed 
    // at the bottom of the screen
    gui_ButtonBar();
}

/*
 * gui_ButtonBar
 * Draws the button bar at the bottom of the screen according 
 * to the current function of each of the 4 Soft Buttons. It
 * also scans for Touch Input for each button, and calls the
 * same function that the button would
 */
void gui_ButtonBar(void){
    Rectangle buttonRectangle = {0,0,0,0};
    DrawTexture(ButtonBarTexture,0,213,WHITE);
    // Button A
    buttonRectangle.x = 0;
    buttonRectangle.y = 213;
    buttonRectangle.width = 80;
    buttonRectangle.height = 17;
	
    if (CheckCollisionPointRec(touchPosition, buttonRectangle) && (currentGesture == GESTURE_TAP)){
        btnA_state = 1;
		currentGesture = GESTURE_NONE;
    }
    // Highlight the button
    if (CheckCollisionPointRec(touchPosition, buttonRectangle) && (currentGesture != GESTURE_NONE)){
        DrawRectangleLines(buttonRectangle.x+1, buttonRectangle.y+3, buttonRectangle.width-3, buttonRectangle.height+4, CLR_DARKBLUE);
        DrawRectangleLines(buttonRectangle.x+2, buttonRectangle.y+4, buttonRectangle.width-5, buttonRectangle.height+2, CLR_DARKBLUE);
    }

    switch(btnA_func){
        case btnA_quit:
            DrawText("Quit",17,217,20,DARKGRAY);
            if (btnA_state == 1){
                btnA_state = 0;
                prog_running = 0;
            }

        break;
        case btnA_select:
            DrawText("SEL",17,217,20,DARKGRAY);
        case btnA_none:
        default:
        break;
    }
    // Button B
    buttonRectangle.x = 80;
    buttonRectangle.y = 213;
    buttonRectangle.width = 80;
    buttonRectangle.height = 17;
    if (CheckCollisionPointRec(touchPosition, buttonRectangle) && (currentGesture == GESTURE_TAP)){
        btnB_state = 1;
		currentGesture = GESTURE_NONE;
    }
    // Highlight the button
    if (CheckCollisionPointRec(touchPosition, buttonRectangle) && (currentGesture != GESTURE_NONE)){
        DrawRectangleLines(buttonRectangle.x+1, buttonRectangle.y+3, buttonRectangle.width-3, buttonRectangle.height+4, CLR_DARKBLUE);
        DrawRectangleLines(buttonRectangle.x+2, buttonRectangle.y+4, buttonRectangle.width-5, buttonRectangle.height+2, CLR_DARKBLUE);
    }
    switch(btnB_func){
        case btnB_menu:
            DrawText("Menu",95,217,20,DARKGRAY);
            if (btnB_state == 1){
                btnB_state = 0;
                ActiveOverlays ^= ovl_MainMenu;
                if(ActiveOverlays & ovl_MainMenu){
                    encoder_focus = menu_on;
                }
            }
        break;
        case btnB_open:
            DrawText("Open",95,217,20,DARKGRAY);
        break;
        case btnB_save:
            DrawText("Save",95,217,20,DARKGRAY);
            if (btnB_state == 1){
                btnB_state = 0;
                //Check what we're saving...
                if(ActiveOverlays & ovl_FileSaveAs){
                    ClearScreenOverlays();
                    buttonsDefault();
                    ClearMenus();
                    MenuSelectItem(0,0);
                    sprintf(current_filename,"resources/sequences/%s",input_txt);
                    FILE * file = fopen(current_filename,"wb");
                    if (file != NULL) {
                        fwrite(&Europi,sizeof(struct europi),1,file);
                        fclose(file);
                        log_msg("Saved as %s",current_filename);
                    }
                    else{
                        log_msg("Error saving as: %s\n",current_filename);
                    }
                }
            }
        break;
        case btnB_cancel:
            DrawText("Cancel",86,217,20,DARKGRAY);
            if ((ActiveOverlays & ovl_ModalDialog) && (btnB_state == 1)){
                btnB_state = 0;
                // Cancel Modal Dialog
                ClearScreenOverlays();
                buttonsDefault();
                ClearMenus();
                MenuSelectItem(0,0);
            }
        break;
        case btnB_val_down:
            DrawText("Val -",95,217,20,DARKGRAY);
        break;
        case btnB_prev:
            DrawText("Prev",95,217,20,DARKGRAY);
        break;
        case btnB_tr_minus:
            DrawText("Trk-",95,217,20,DARKGRAY);
        break;
        case btnB_none:
        default:
        break;
    }
    // Button C
    buttonRectangle.x = 160;
    buttonRectangle.y = 213;
    buttonRectangle.width = 80;
    buttonRectangle.height = 17;
    if (CheckCollisionPointRec(touchPosition, buttonRectangle) && (currentGesture == GESTURE_TAP)){
        btnC_state = 1;
		currentGesture = GESTURE_NONE;
    }
    // Highlight the button
    if (CheckCollisionPointRec(touchPosition, buttonRectangle) && (currentGesture != GESTURE_NONE)){
        DrawRectangleLines(buttonRectangle.x+1, buttonRectangle.y+3, buttonRectangle.width-3, buttonRectangle.height+4, CLR_DARKBLUE);
        DrawRectangleLines(buttonRectangle.x+2, buttonRectangle.y+4, buttonRectangle.width-5, buttonRectangle.height+2, CLR_DARKBLUE);
    }
    switch(btnC_func){
        case btnC_bpm_dn:
            DrawText("BPM-",177,217,20,DARKGRAY);
            if (btnC_state == 1){
                btnC_state = 0;
                clock_freq -= 10;
                if (clock_freq < 1) clock_freq = 1;
                gpioHardwarePWM(MASTER_CLK,clock_freq,500000);
                // Display the current BPM on a floating overlay
                // and launch a timed Thread to turn it off
                ActiveOverlays |= ovl_BPM;  // Display BPM Overlay
                struct ovl_timer sOvlTimer; 
                sOvlTimer.sleeptime = 500000;
                sOvlTimer.overlays = ~ovl_BPM;
                struct ovl_timer *pOvlTimer = malloc(sizeof(struct ovl_timer));
                memcpy(pOvlTimer, &sOvlTimer, sizeof(struct ovl_timer));
                if(pthread_create(&ThreadId, &detached_attr, &OvlTimerThread,pOvlTimer)){
                log_msg("OvlTimer thread creation error\n");
                }
            }
        break;
        case btnC_OK:
            DrawText("OK",186,217,20,DARKGRAY);
            if (btnC_state == 1){
                btnC_state = 0;
                // Don't know what we're cancelling, and don't care
                ClearScreenOverlays();
                buttonsDefault();
                ClearMenus();
                MenuSelectItem(0,0);
            }
        break;
        case btnC_cancel:
            DrawText("Cancel",167,217,20,DARKGRAY);
            if (btnC_state == 1){
                btnC_state = 0;
                // Don't know what we're cancelling, and don't care
                ClearScreenOverlays();
                buttonsDefault();
                ClearMenus();
                MenuSelectItem(0,0);  
            }
        break;
        case btnC_val_up:
            DrawText("Val +",167,217,20,DARKGRAY);
        break;
        case btnC_next:
            DrawText("Next",178,217,20,DARKGRAY);
        break;
        case btnC_tr_plus:
            DrawText("Trk+",178,217,20,DARKGRAY);
        break;
        case btnC_none:
        default:
        break;
    }
    // Button D
    buttonRectangle.x = 240;
    buttonRectangle.y = 213;
    buttonRectangle.width = 80;
    buttonRectangle.height = 17;
    if (CheckCollisionPointRec(touchPosition, buttonRectangle) && (currentGesture == GESTURE_TAP)){
        btnD_state = 1;
		currentGesture = GESTURE_NONE;
    }
    // Highlight the button
    if (CheckCollisionPointRec(touchPosition, buttonRectangle) && (currentGesture != GESTURE_NONE)){
        DrawRectangleLines(buttonRectangle.x+1, buttonRectangle.y+3, buttonRectangle.width-3, buttonRectangle.height+4, CLR_DARKBLUE);
        DrawRectangleLines(buttonRectangle.x+2, buttonRectangle.y+4, buttonRectangle.width-5, buttonRectangle.height+2, CLR_DARKBLUE);
    }
    switch(btnD_func){
        case btnD_bpm_up:
            DrawText("BPM+",257,217,20,DARKGRAY);
            if (btnD_state == 1){
                btnD_state = 0;
                clock_freq += 10;
                gpioHardwarePWM(MASTER_CLK,clock_freq,500000);
                // Display the current BPM on a floating overlay
                // and launch a timed Thread to turn it off
                ActiveOverlays |= ovl_BPM;  // Display BPM Overlay
                struct ovl_timer sOvlTimer; 
                sOvlTimer.sleeptime = 500000;
                sOvlTimer.overlays = ~ovl_BPM;
                struct ovl_timer *pOvlTimer = malloc(sizeof(struct ovl_timer));
                memcpy(pOvlTimer, &sOvlTimer, sizeof(struct ovl_timer));
                if(pthread_create(&ThreadId, &detached_attr, &OvlTimerThread,pOvlTimer)){
                log_msg("OvlTimer thread creation error\n");
                }
            }
        break;
        case btnD_done:
            DrawText("Done",257,217,20,DARKGRAY);
            if (btnD_state == 1){
                btnD_state = 0;
                // Don't know what we're done doing, but don't care
                if(DisplayPage == SingleStep) DisplayPage = GridView;
                if(DisplayPage == SingleAD) DisplayPage = GridView;
                if(DisplayPage == SingleADSR) DisplayPage = GridView;
                if(DisplayPage == SingleChannel) DisplayPage = GridView;
                ClearScreenOverlays();
                buttonsDefault();
                ClearMenus();
                MenuSelectItem(0,0);
                run_stop = save_run_stop;   // Restores the previous run_stop state
				currentGesture = GESTURE_NONE;
            }

        case btnD_none:
        default:
        break;
    }
}

void gui_MainMenu(void){
    int x = 5;
    int txt_len;
    int PanelHeight = MENU_FONT_SIZE + MENU_TB_MARGIN;
    Color menu_colour;
    Rectangle menuRectangle = {0,0,0,0}; 
    // Top Bar
    DrawTexture(TopBarTexture,0,0,WHITE);
    int i = 0;
    while(Menu[i].name != NULL){
        txt_len = MeasureText(Menu[i].name,MENU_FONT_SIZE);
        //Draw a box a bit bigger than this
        if (Menu[i].highlight == 1) menu_colour = CLR_LIGHTBLUE; else menu_colour = CLR_DARKBLUE;
        menuRectangle.x = x;
        menuRectangle.y = 2;
        menuRectangle.width = txt_len+(MENU_LR_MARGIN * 2);
        menuRectangle.height = PanelHeight;
        if (CheckCollisionPointRec(touchPosition, menuRectangle) && (currentGesture == GESTURE_TAP)){
            // Toggle the expansion of this menu item
            if (Menu[i].highlight == 0) {
                // this Menu item not currently highlighted, so
                // de-hilight the existing one, and highlight this
                int m = 0;
                while(Menu[m].name != NULL){
                    Menu[m].highlight = 0;
                    Menu[m].expanded = 0;
                    m++;
                }
                Menu[i].highlight = 1;
                Menu[m].expanded = 1;
            }
            toggle_menu();
        }
        DrawRectangleRec(menuRectangle,menu_colour);
        DrawText(Menu[i].name,x+MENU_LR_MARGIN,MENU_TOP_MARGIN,MENU_FONT_SIZE,DARKGRAY);
        if(Menu[i].expanded == 1){
            // Draw sub-menus
            int j = 0;
            int y = PanelHeight;
            int sub_len = 0;
            int tmp_len;
            // Measure the length of the longest sub menu
            while(Menu[i].child[j]->name != NULL){
                tmp_len = MeasureText(Menu[i].child[j]->name,MENU_FONT_SIZE);
                if(tmp_len > sub_len) sub_len = tmp_len;
                j++;
            }
            j = 0;
            while(Menu[i].child[j]->name != NULL){
                if (Menu[i].child[j]->highlight == 1) menu_colour = CLR_LIGHTBLUE; else menu_colour = CLR_DARKBLUE;
                // Deal with the direction this leaf opens
                switch (Menu[i].child[j]->direction){
                    case dir_right:
                        menuRectangle.x = x;
                    break;
                    case dir_left:
                        menuRectangle.x = x + txt_len - sub_len;
                    break;
                    default:
                        menuRectangle.x = x;
                    break;
                }
                menuRectangle.y = y;
                menuRectangle.width = sub_len+(MENU_LR_MARGIN * 2);
                menuRectangle.height = PanelHeight;
                if (CheckCollisionPointRec(touchPosition, menuRectangle) && (currentGesture == GESTURE_TAP)){
                    // Call function pointed to by this menu item
                    MenuSelectItem(i,j);
                    if (Menu[i].child[j]->funcPtr != NULL) Menu[i].child[j]->funcPtr();
                }
                DrawRectangleRec(menuRectangle,menu_colour);
                DrawText(Menu[i].child[j]->name,menuRectangle.x+MENU_LR_MARGIN,y+MENU_TB_MARGIN,MENU_FONT_SIZE,DARKGRAY);
                y+=PanelHeight;
                j++;
            }
        }
        x+=txt_len+(MENU_LR_MARGIN * 2)+MENU_HORIZ_SPACE;
        i++;
    }
}

/*
* gui_debug()
* if the global variable debug is set == TRUE
* then this will display debug messages on top of
* whatever else is going on on the screen. This
* starts at the oldest message (ie the one that
* will be overwritten next) that way the most recent
* message will always be at the bottom of the screen
*/
void gui_debug(void){
    if(debug == FALSE) return;
    int i;
    int current_row = next_debug_slot;
    DrawRectangle(5,100,310,112,WHITE);
    for(i = 0; i <10; i++){
        DrawText(debug_messages[current_row++],7,104+(i*11),10,BLACK);
        if(current_row >= 10) current_row = 0;
    }
}
